falkien/Sunlu_S8_Switchwire_Conversion/Pics/Front Skirt.jpg

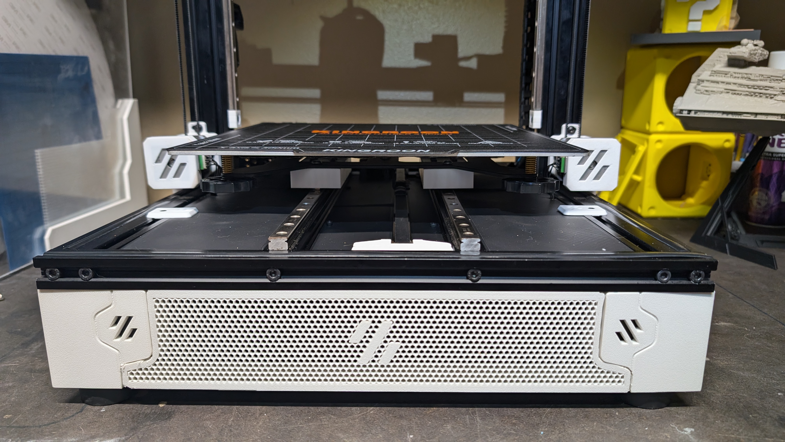
Pics/Front Skirt.jpg
