falkien/Sunlu_S8_Switchwire_Conversion/Pics/Overhead No Bed 4.jpg

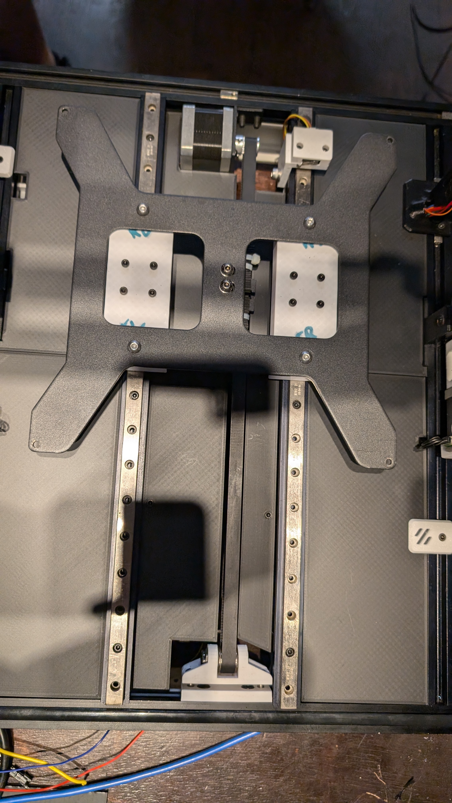
Pics/Overhead No Bed 4.jpg
