falkien/Sunlu_S8_Switchwire_Conversion/Pics/Overhead No Bed Rear 2.jpg

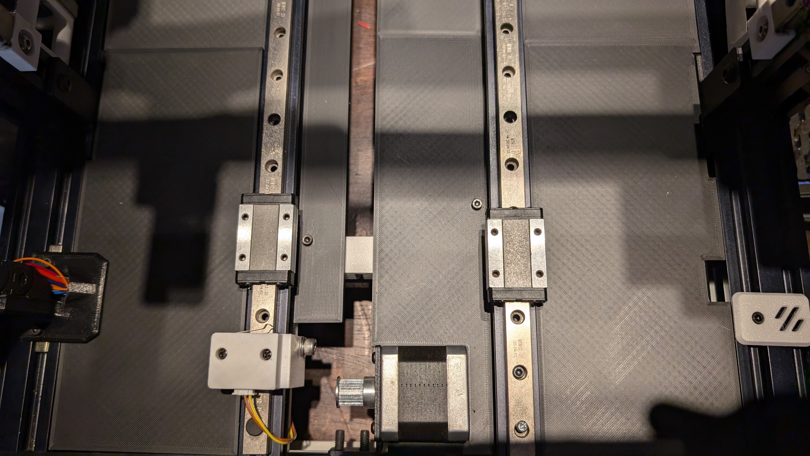
Pics/Overhead No Bed Rear 2.jpg
