falkien/Sunlu_S8_Switchwire_Conversion/Pics/Overhead No Bed Rear.jpg

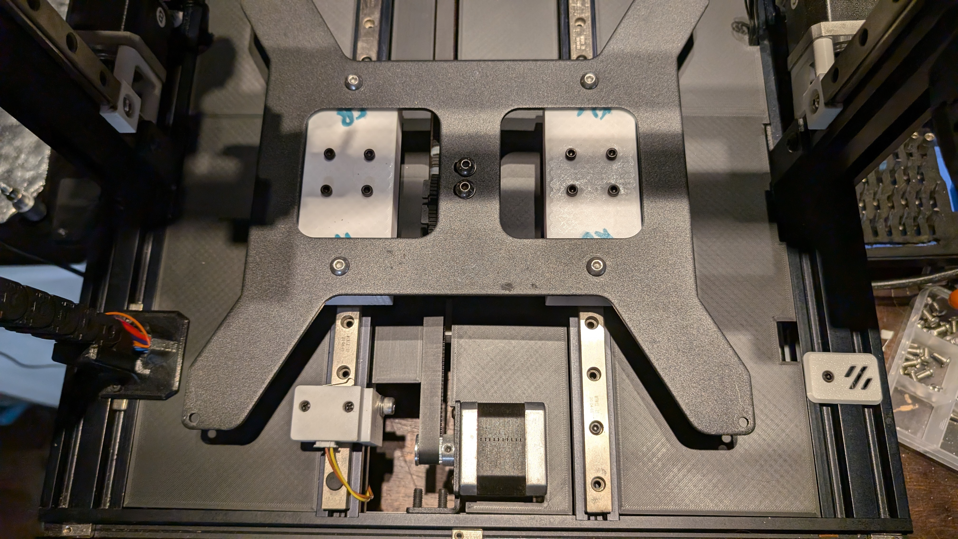
Pics/Overhead No Bed Rear.jpg
