falkien/Sunlu_S8_Switchwire_Conversion/Pics/Real All.jpg

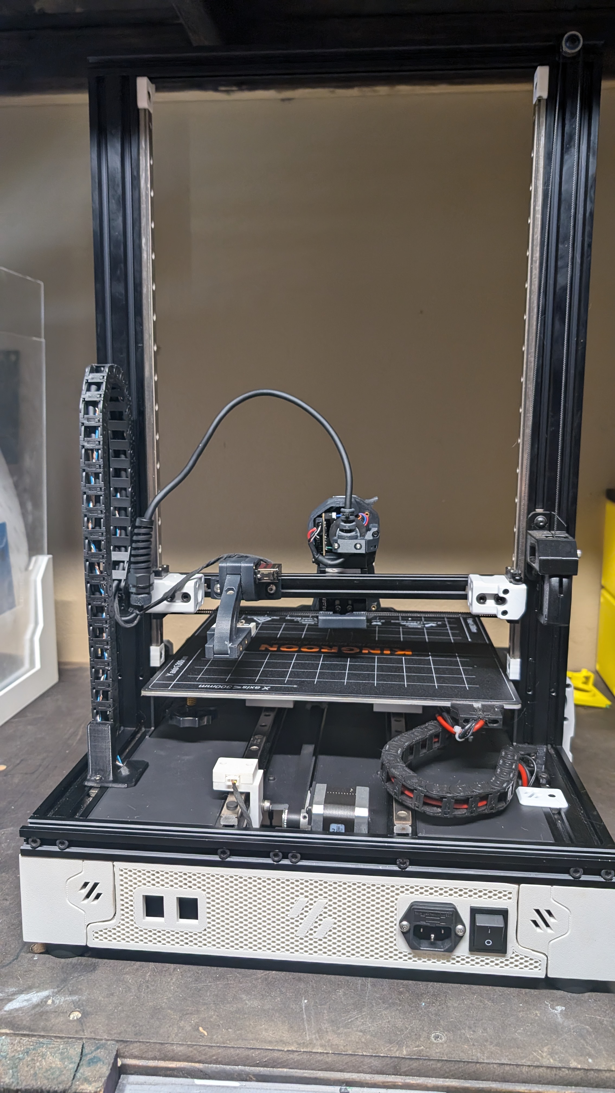
Pics/Real All.jpg
