falkien/Sunlu_S8_Switchwire_Conversion/Pics/Rear left.jpg

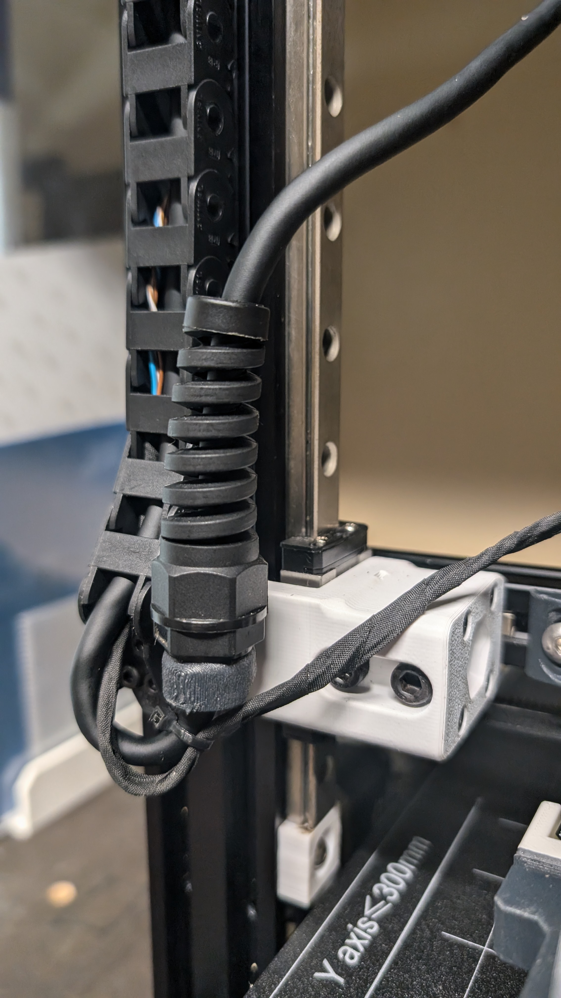
Pics/Rear left.jpg
