falkien/Sunlu_S8_Switchwire_Conversion/Pics/Rear Lower Chain.jpg

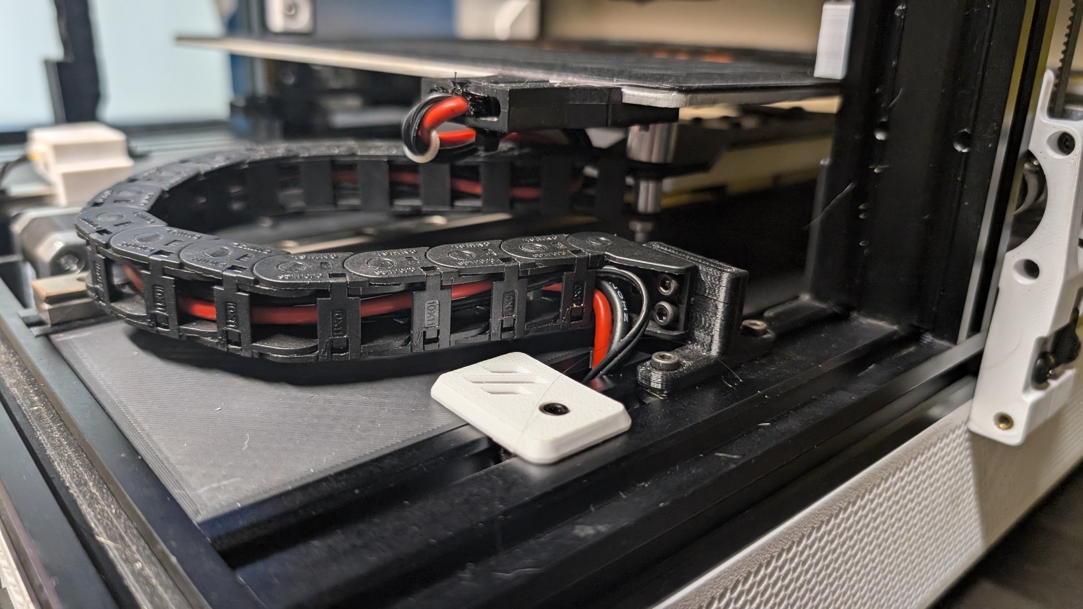
Pics/Rear Lower Chain.jpg
