falkien/Sunlu_S8_Switchwire_Conversion/Pics/Rear Skirt.jpg

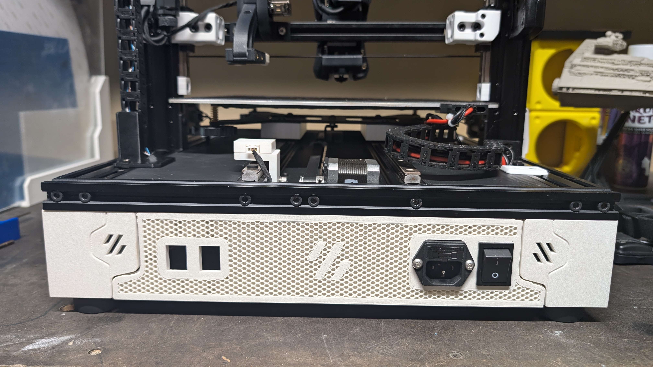
Pics/Rear Skirt.jpg
