falkien/Sunlu_S8_Switchwire_Conversion/Pics/Rear Toolhead Wide.jpg

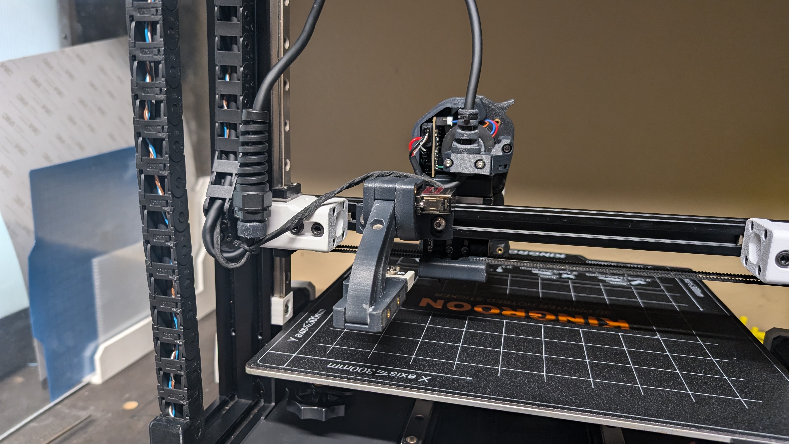
Pics/Rear Toolhead Wide.jpg
