falkien/Sunlu_S8_Switchwire_Conversion/Pics/Rear Toolhead.jpg

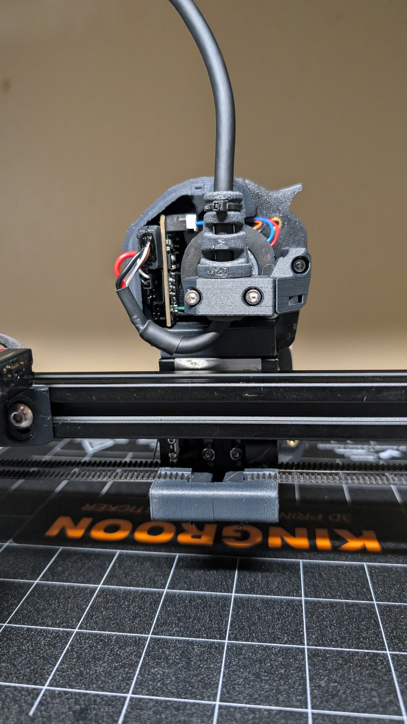
Pics/Rear Toolhead.jpg
