falkien/Sunlu_S8_Switchwire_Conversion/Pics/Rear Verticle Chain.jpg

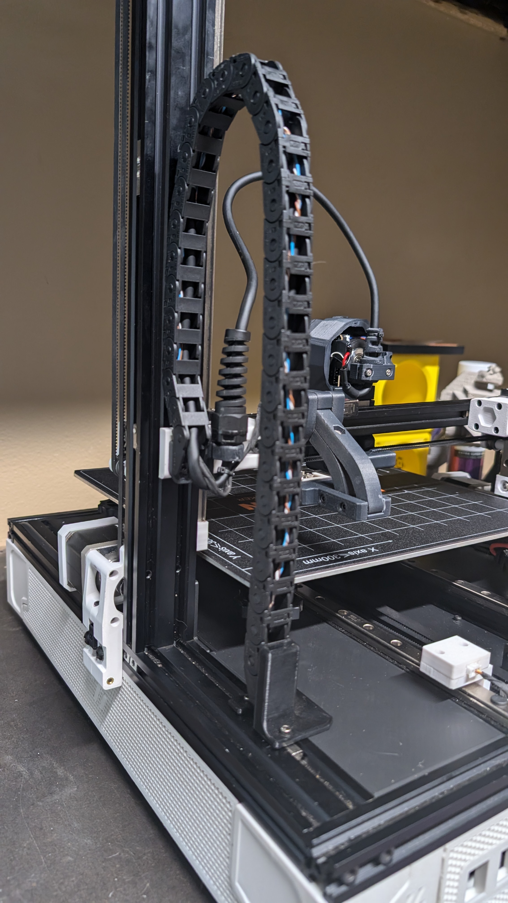
Pics/Rear Verticle Chain.jpg
