falkien/Sunlu_S8_Switchwire_Conversion/Pics/Right Main.jpg

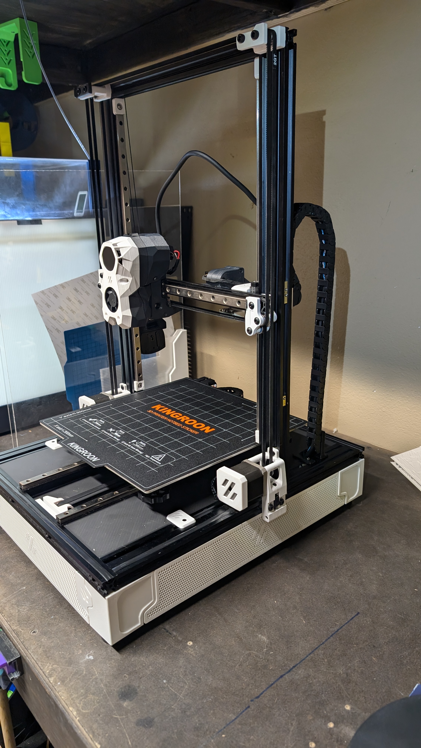
Pics/Right Main.jpg
