falkien/Sunlu_S8_Switchwire_Conversion/Pics/Right Skirt.jpg

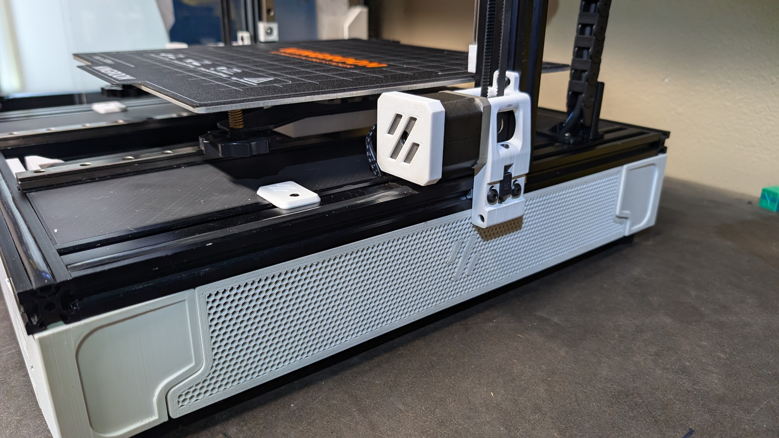
Pics/Right Skirt.jpg
