falkien/Sunlu_S8_Switchwire_Conversion/STL's/X axis/Swichwire_reverse_bowden_.stl

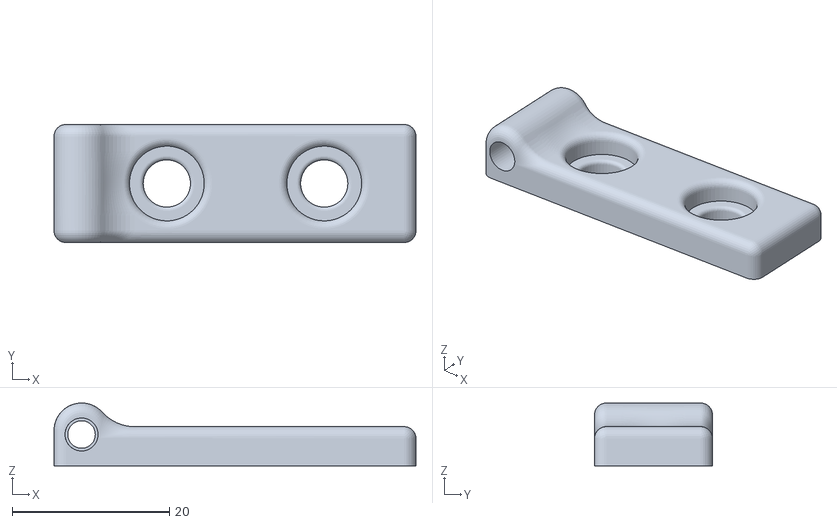
[picture p37: CAD file, 2024-08-12]
STL's/X axis/Swichwire_reverse_bowden_.stl
46.0 x 15.0 x 8.00
