falkien/Sunlu_S8_Switchwire_Conversion/STL's/Y axis/Sunlu_Y_Axis_rail_adaptor.stl

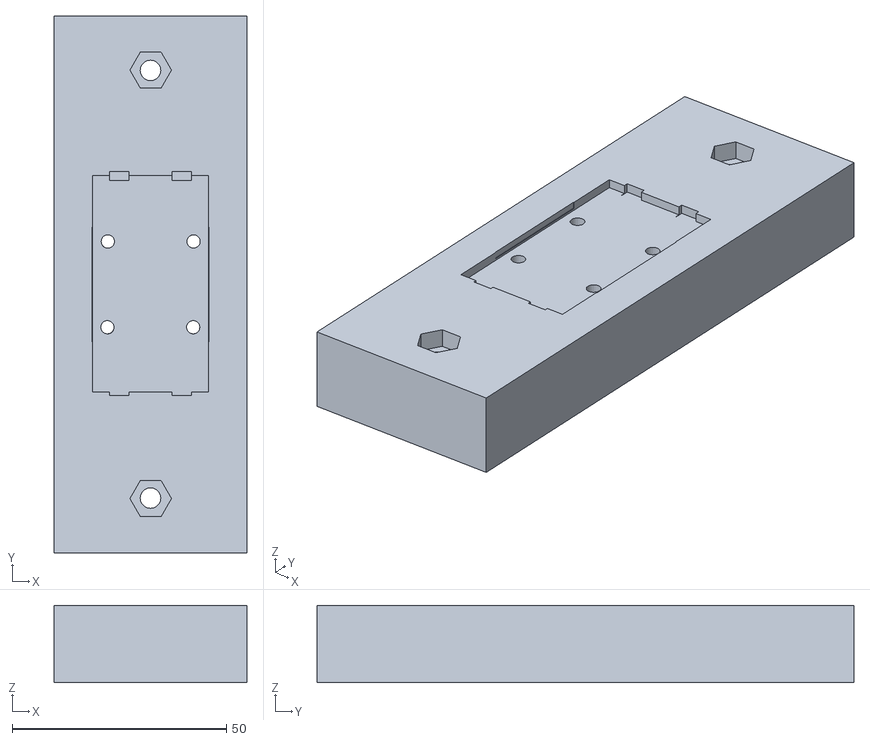
[picture p38: CAD file, 2024-01-11]
STL's/Y axis/Sunlu_Y_Axis_rail_adaptor.stl
45.0 x 125.2 x 18.0
