falkien/Sunlu_S8_Switchwire_Conversion/STL's/Z axis/keybak_mount_plate_b.stl

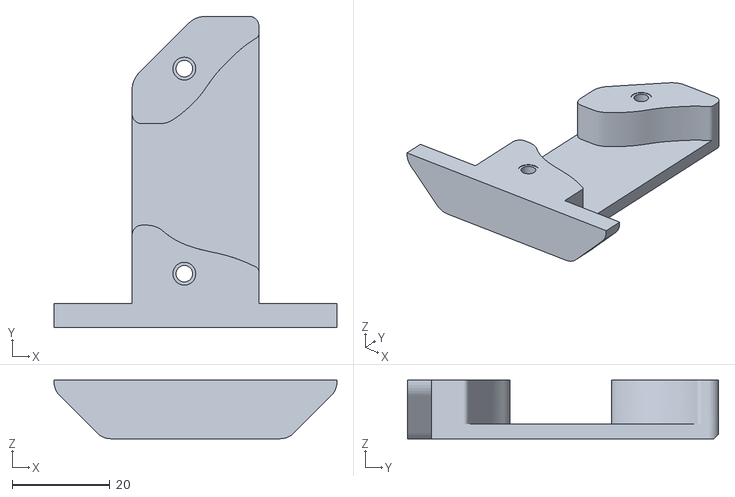
[picture p39: CAD file, 2024-01-11]
STL's/Z axis/keybak_mount_plate_b.stl
58.0 x 63.8 x 12.0
