falkien/Sunlu_S8_Switchwire_Conversion/STL's/Electronic Covers/Switchwire_Sunlu_S8_Left_Center.step

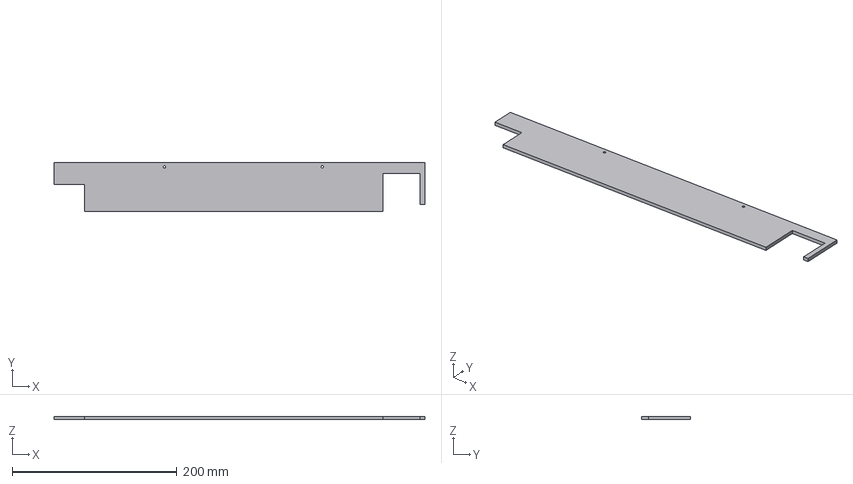
[picture p40: CAD file, 2024-08-11]
STL's/Electronic Covers/Switchwire_Sunlu_S8_Left_Center.step
450.0 x 60.0 x 4.00 mm
