falkien/Sunlu_S8_Switchwire_Conversion/STL's/Electronics_Bay/RPI fan mount bottom.stl

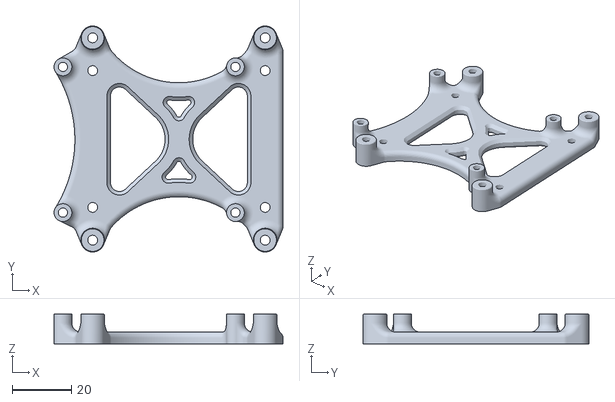
[picture p41: CAD file, 2024-08-12]
STL's/Electronics_Bay/RPI fan mount bottom.stl
77.0 x 76.0 x 10.0
