falkien/Sunlu_S8_Switchwire_Conversion/STL's/Skirt_New/Sunlu-S8_Switchwire-front-noscreen_274.1mm.3mf

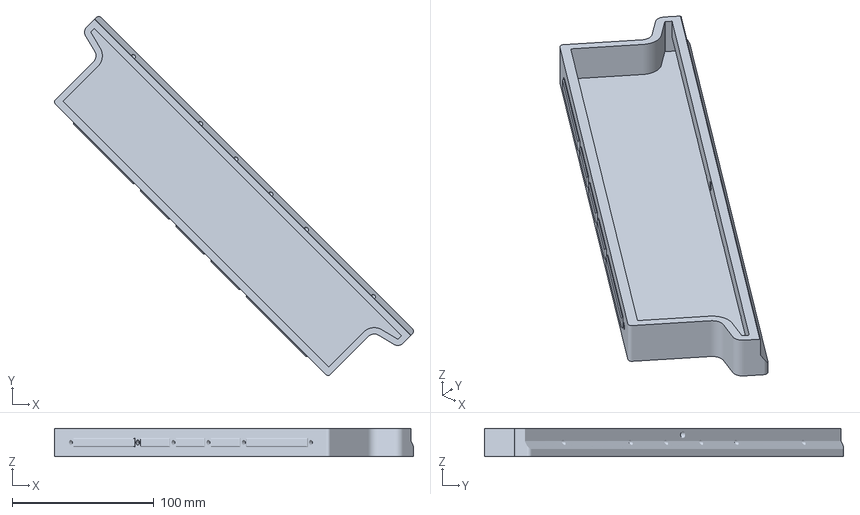
[picture p42: CAD file, 2024-07-28]
STL's/Skirt_New/Sunlu-S8_Switchwire-front-noscreen_274.1mm.3mf
253.2 x 253.2 x 20.0 mm
