falkien/Sunlu_S8_Switchwire_Conversion/STL's/Stealthburner/[o]_stealthburner_LED_diffuser_mask.stl

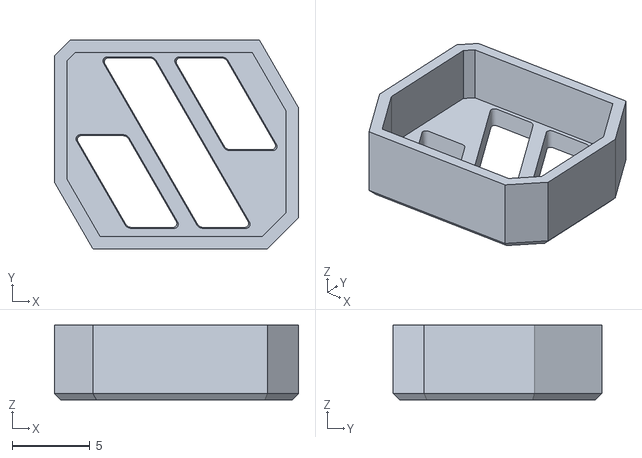
[picture p43: CAD file, 2024-01-11]
STL's/Stealthburner/[o]_stealthburner_LED_diffuser_mask.stl
15.7 x 13.4 x 4.80
