falkien/Sunlu_S8_Switchwire_Conversion/STL's/Stealthburner/ADXL345_Mounts/sb_adxl_mount_adafruit_19mm_c_c.stl

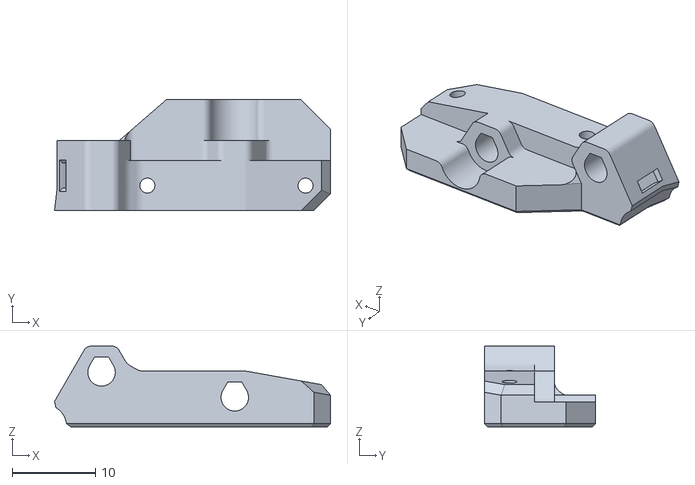
[picture p44: CAD file, 2024-01-11]
STL's/Stealthburner/ADXL345_Mounts/sb_adxl_mount_adafruit_19mm_c_c.stl
33.2 x 13.4 x 9.70
