falkien/Sunlu_S8_Switchwire_Conversion/STL's/Toolhead_Cable_Management/cw2-pug-mount-arm.3mf

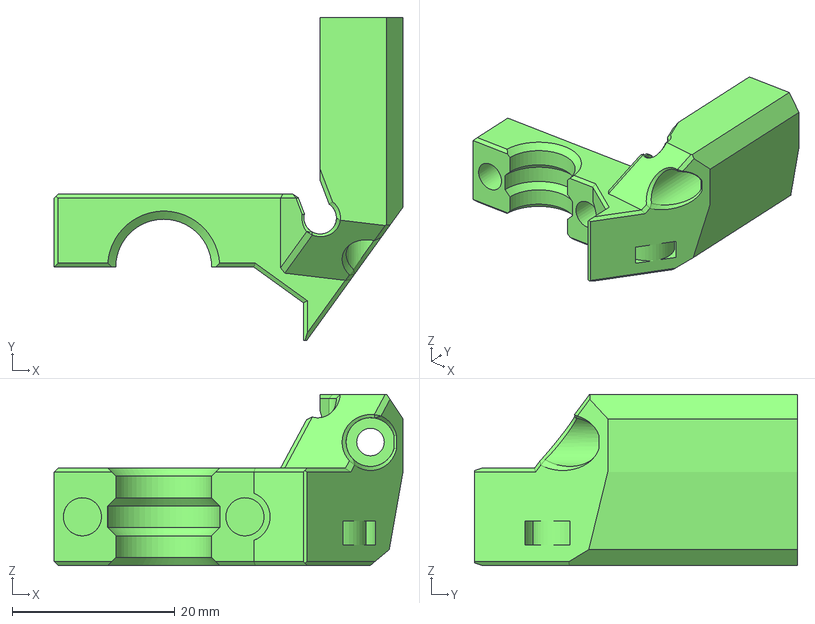
[picture p45: CAD file, 2024-08-12]
STL's/Toolhead_Cable_Management/cw2-pug-mount-arm.3mf
42.9 x 39.7 x 21.1 mm
