falkien/Sunlu_S8_Switchwire_Conversion/STL's/X axis/Knomi Screen/StealthBurner Mounting Plate for KNOMI.STL

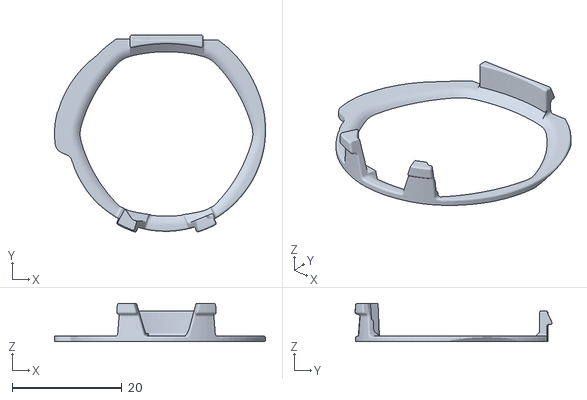
[picture p46: CAD file, 2024-01-11]
STL's/X axis/Knomi Screen/StealthBurner Mounting Plate for KNOMI.STL
38.4 x 35.8 x 7.00
