falkien/Sunlu_S8_Switchwire_Conversion/STL's/X axis/xz_block_right_b.stl

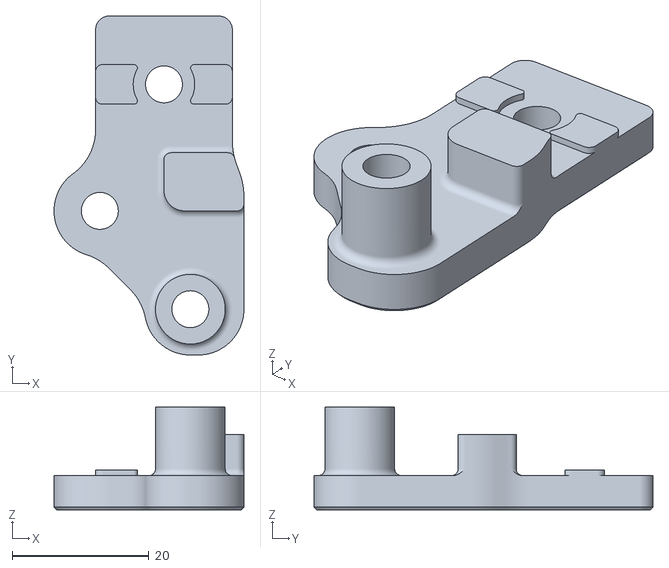
[picture p47: CAD file, 2024-01-11]
STL's/X axis/xz_block_right_b.stl
27.8 x 49.6 x 15.0
