falkien/Sunlu_S8_Switchwire_Conversion/STL's/Y axis/Sunlu_Y-Axis_Brkt_V1.stl

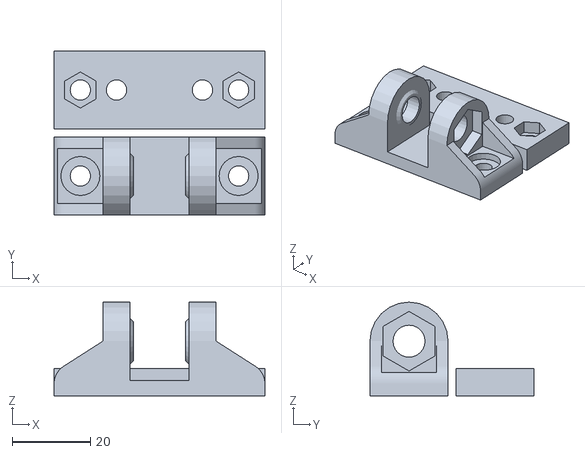
[picture p48: CAD file, 2024-01-11]
STL's/Y axis/Sunlu_Y-Axis_Brkt_V1.stl
54.0 x 42.0 x 24.0
