falkien/Sunlu_S8_Switchwire_Conversion/STL's/Z axis/Nema17 Motor Cover - Voron Logo for SW_inserted_90.stl

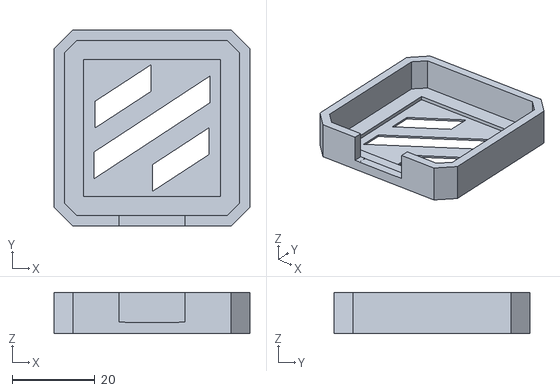
[picture p49: CAD file, 2024-01-11]
STL's/Z axis/Nema17 Motor Cover - Voron Logo for SW_inserted_90.stl
47.3 x 47.3 x 10.00
