falkien/Sunlu_S8_Switchwire_Conversion/STL's/Electronic Covers/Switchwire_Sunlu_S8_Right_Center.step

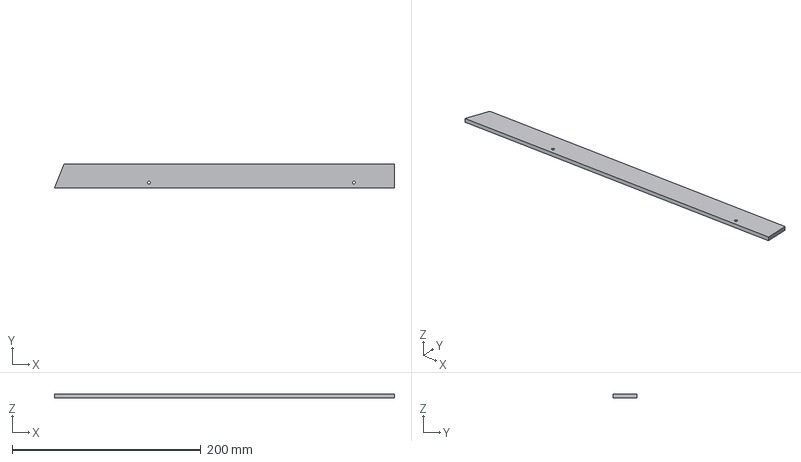
[picture p50: CAD file, 2024-08-11]
STL's/Electronic Covers/Switchwire_Sunlu_S8_Right_Center.step
360.0 x 25.0 x 4.00 mm
