falkien/Sunlu_S8_Switchwire_Conversion/STL's/Electronics_Bay/CableDuctCover_small.stl

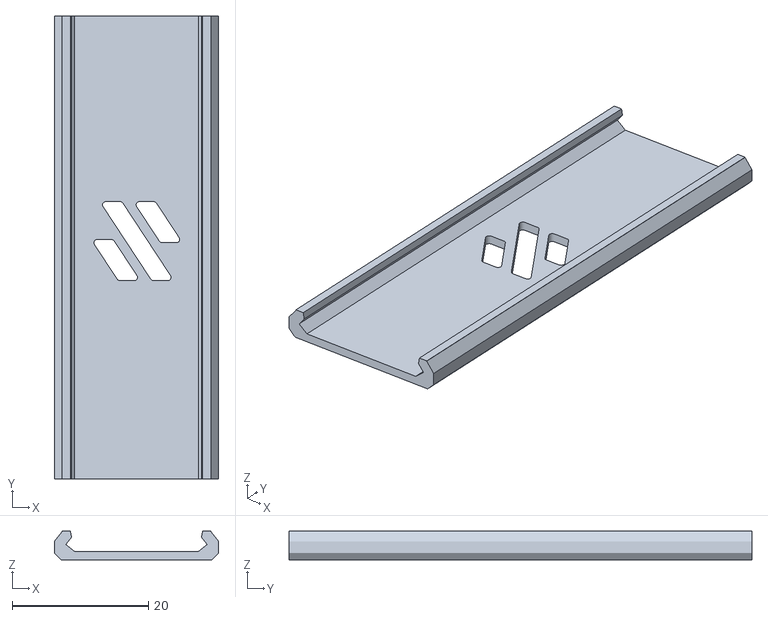
[picture p51: CAD file, 2024-08-12]
STL's/Electronics_Bay/CableDuctCover_small.stl
24.1 x 68.0 x 4.20
