falkien/Sunlu_S8_Switchwire_Conversion/STL's/Skirt_New/Sunlu-S8_Switchwire-Front-BTT-TFT50-V2_1x.3mf

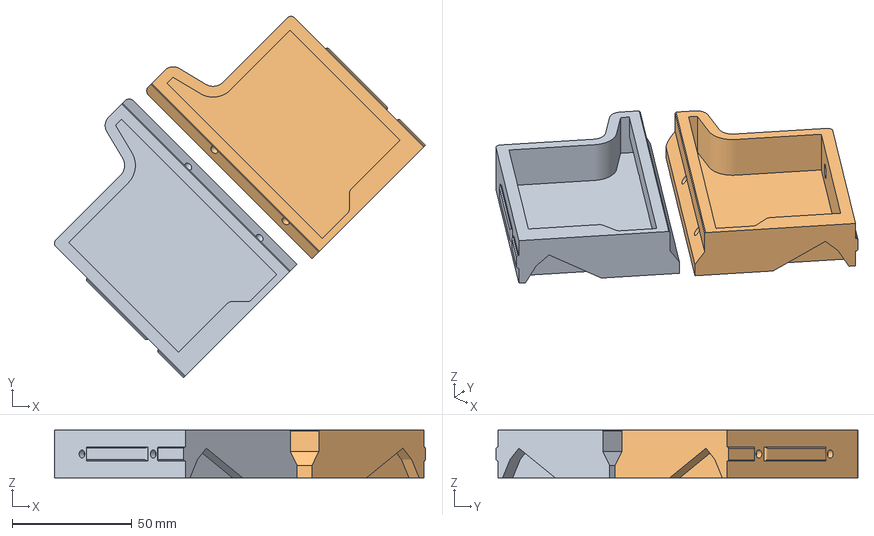
[picture p52: CAD file, 2024-07-27]
STL's/Skirt_New/Sunlu-S8_Switchwire-Front-BTT-TFT50-V2_1x.3mf
154.9 x 150.9 x 20.0 mm
Front-TFT50-A-250
Front-TFT50-B-250
