falkien/Sunlu_S8_Switchwire_Conversion/STL's/Stealthburner/[c]_stealthburner_LED_diffuser.stl

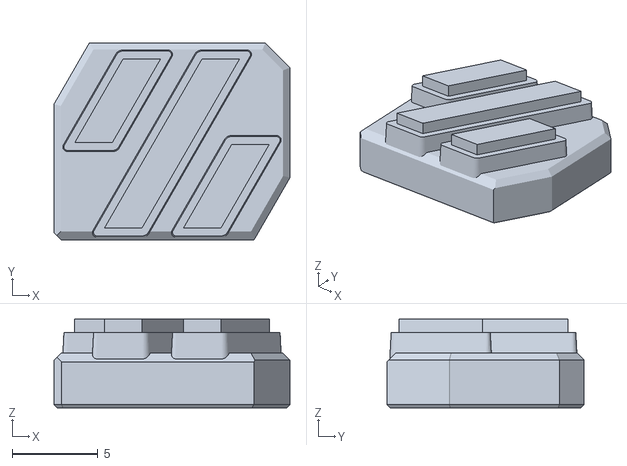
[picture p53: CAD file, 2024-01-11]
STL's/Stealthburner/[c]_stealthburner_LED_diffuser.stl
13.8 x 11.5 x 5.20
