falkien/Sunlu_S8_Switchwire_Conversion/STL's/Toolhead_Cable_Management/pug_v4_s_70mm.stl

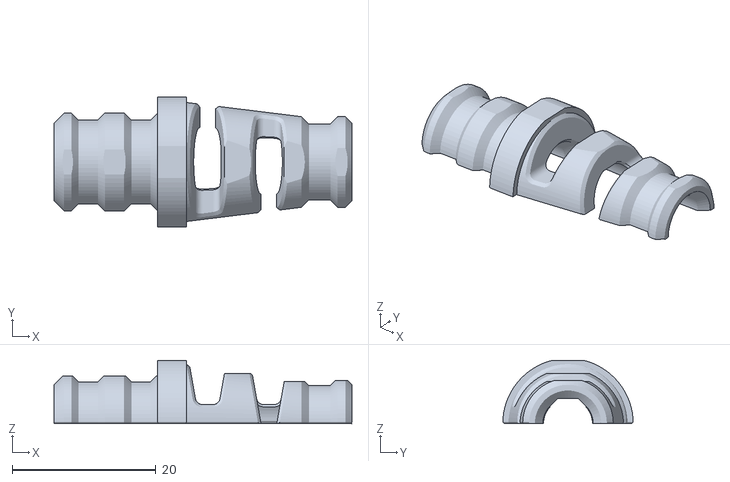
[picture p54: CAD file, 2024-08-12]
STL's/Toolhead_Cable_Management/pug_v4_s_70mm.stl
41.4 x 18.1 x 8.80
