falkien/Sunlu_S8_Switchwire_Conversion/STL's/X axis/xz_block_right_a.stl

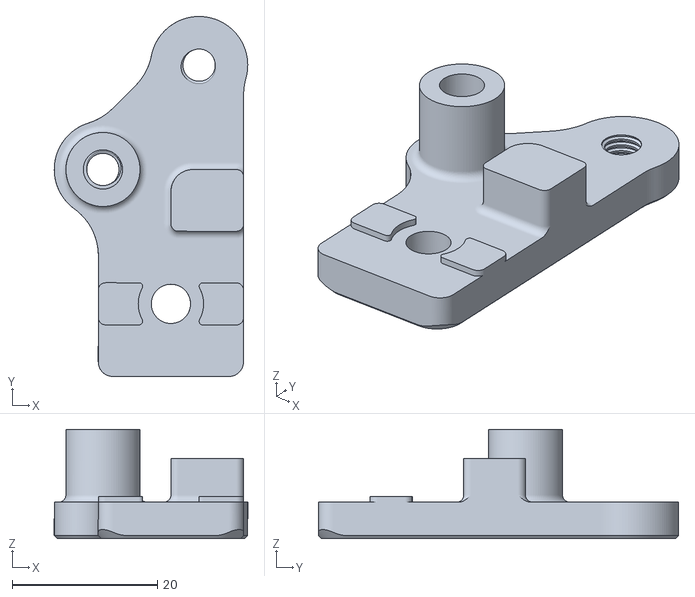
[picture p55: CAD file, 2024-01-11]
STL's/X axis/xz_block_right_a.stl
26.7 x 49.6 x 15.0
