falkien/Sunlu_S8_Switchwire_Conversion/STL's/Y axis/Sunlu_Y_Axis_endstop.stl

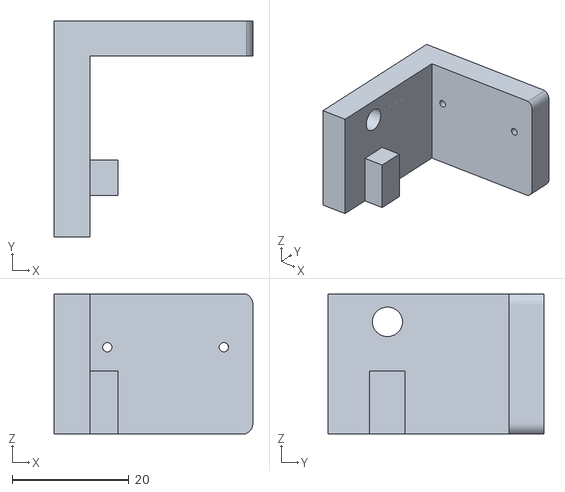
[picture p56: CAD file, 2024-01-11]
STL's/Y axis/Sunlu_Y_Axis_endstop.stl
34.1 x 37.0 x 24.0
