falkien/Sunlu_S8_Switchwire_Conversion/STL's/Z axis/z_motor_mount_a.stl

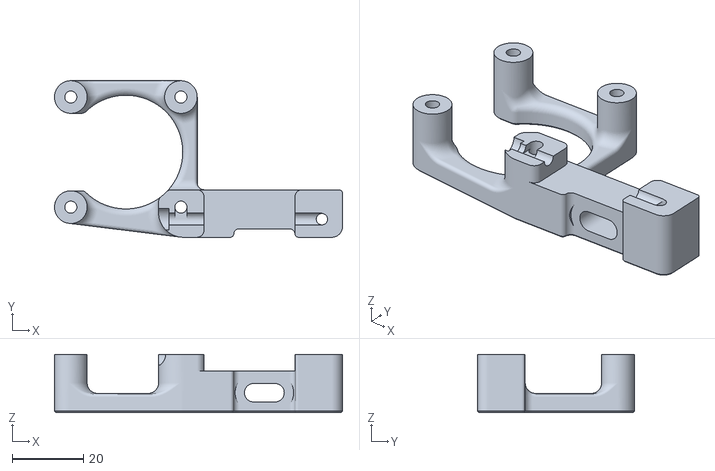
[picture p57: CAD file, 2024-01-11]
STL's/Z axis/z_motor_mount_a.stl
81.1 x 44.1 x 16.4
