falkien/Sunlu_S8_Switchwire_Conversion/STL's/Electronic Covers/Switchwire_Sunlu_S8_Right_Front.step

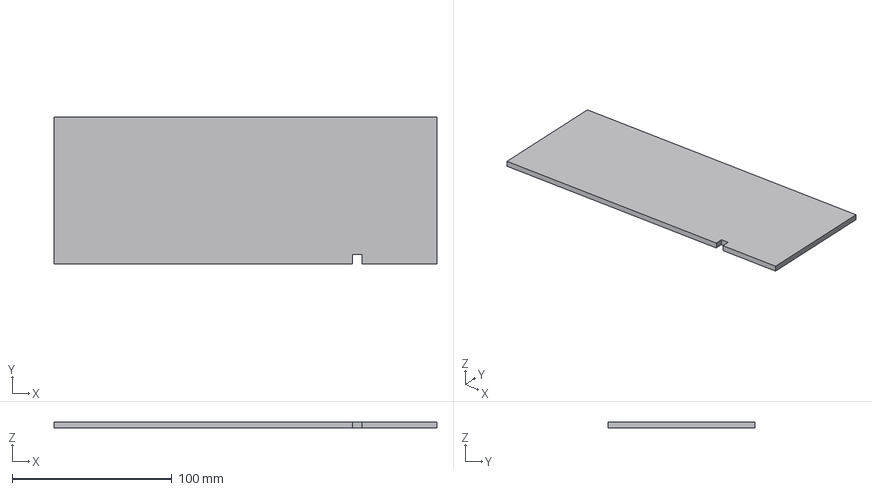
[picture p58: CAD file, 2024-08-11]
STL's/Electronic Covers/Switchwire_Sunlu_S8_Right_Front.step
240.0 x 92.0 x 4.00 mm
