falkien/Sunlu_S8_Switchwire_Conversion/STL's/Electronics_Bay/CableDuctCover_large.stl

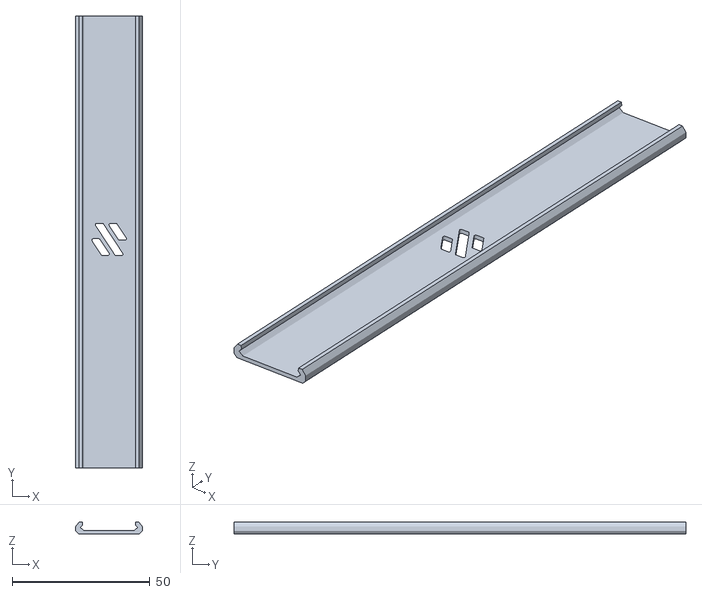
[picture p59: CAD file, 2024-08-12]
STL's/Electronics_Bay/CableDuctCover_large.stl
24.1 x 164.0 x 4.20
