falkien/Sunlu_S8_Switchwire_Conversion/STL's/Skirt_New/Trident-original-Side-skirt-V2-350_2x.3mf

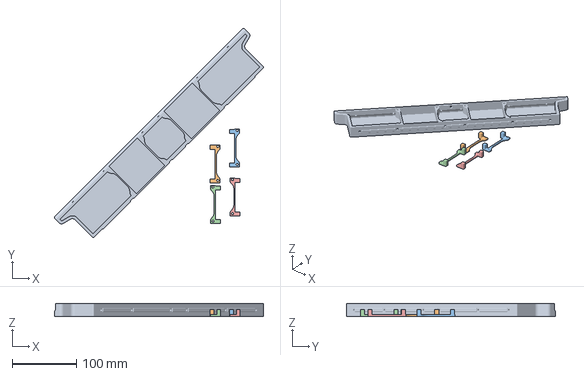
[picture p60: CAD file, 2024-07-27]
STL's/Skirt_New/Trident-original-Side-skirt-V2-350_2x.3mf
324.4 x 324.4 x 20.0 mm
F1-Side-skirt-mid-V1.stl
Side-skirt-fanholder_V2.stl x 4
