falkien/Sunlu_S8_Switchwire_Conversion/STL's/Toolhead_Cable_Management/Support pg7 - 1.stl

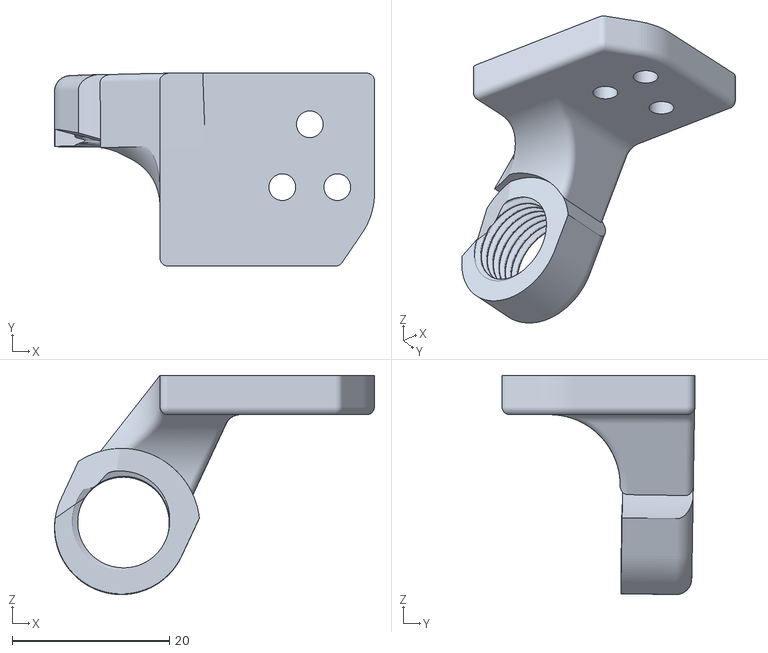
[picture p61: CAD file, 2024-08-12]
STL's/Toolhead_Cable_Management/Support pg7 - 1.stl
40.7 x 24.6 x 27.9
