falkien/Sunlu_S8_Switchwire_Conversion/STL's/Y axis/Sunlu_Y_chain_frame_anchor_igus.stl

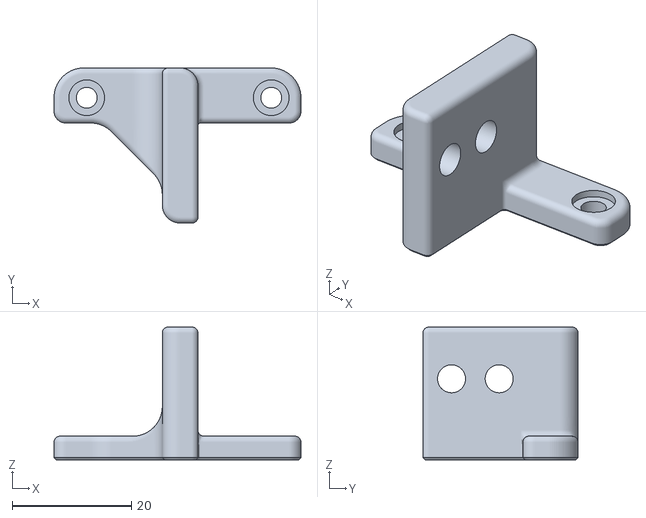
[picture p62: CAD file, 2024-01-11]
STL's/Y axis/Sunlu_Y_chain_frame_anchor_igus.stl
41.5 x 26.1 x 22.3
