falkien/Sunlu_S8_Switchwire_Conversion/STL's/Z axis/z_carriage_stop_V2_x4.stl

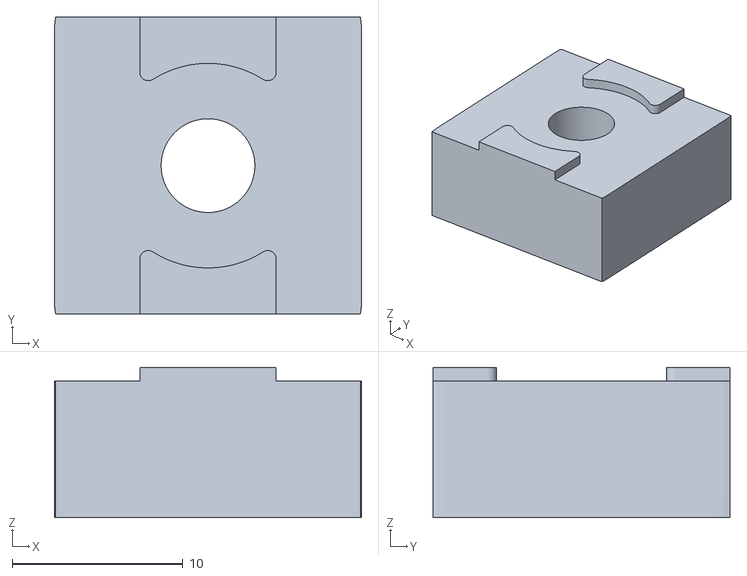
[picture p63: CAD file, 2024-01-11]
STL's/Z axis/z_carriage_stop_V2_x4.stl
18.0 x 17.4 x 8.80
