falkien/Sunlu_S8_Switchwire_Conversion/STL's/Electronic Covers/Switchwire_Sunlu_S8_Left_Rear.step

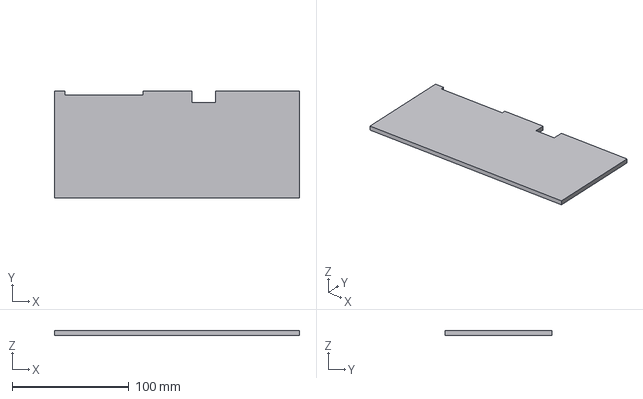
[picture p64: CAD file, 2024-08-11]
STL's/Electronic Covers/Switchwire_Sunlu_S8_Left_Rear.step
210.0 x 92.0 x 4.00 mm
