falkien/Sunlu_S8_Switchwire_Conversion/STL's/Electronics_Bay/CableDuctBody_medium.stl

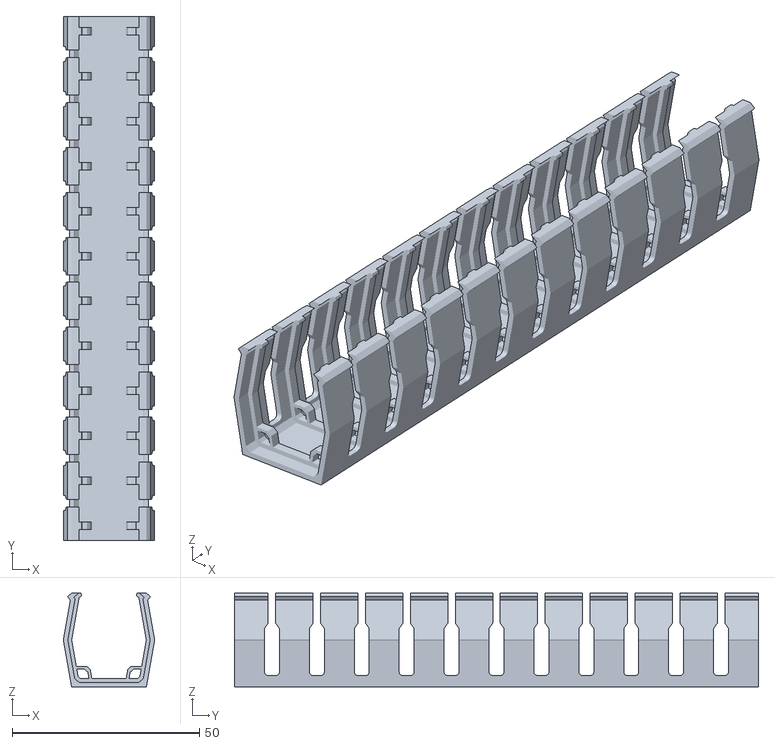
[picture p65: CAD file, 2024-08-12]
STL's/Electronics_Bay/CableDuctBody_medium.stl
24.4 x 140.0 x 25.0
