falkien/Sunlu_S8_Switchwire_Conversion/STL's/Skirt_New/Sunlu-S8_Switchwire-Optional_FootV2-B_2x.stl

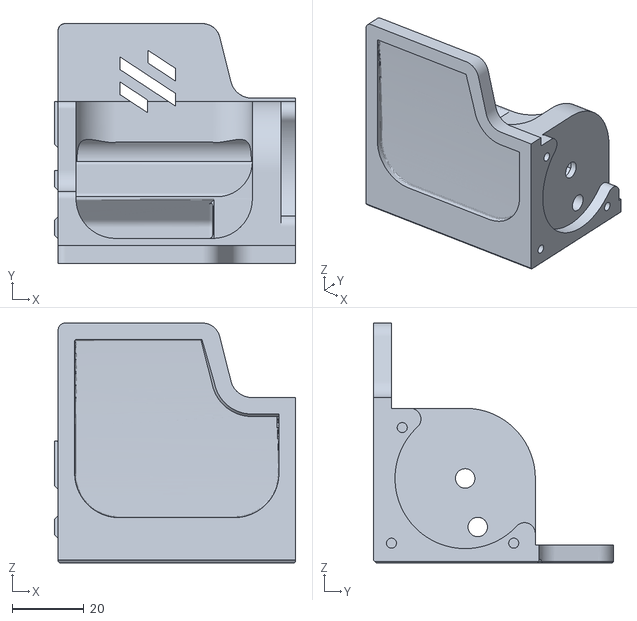
[picture p66: CAD file, 2024-07-27]
STL's/Skirt_New/Sunlu-S8_Switchwire-Optional_FootV2-B_2x.stl
67.0 x 66.7 x 66.7
