falkien/Sunlu_S8_Switchwire_Conversion/STL's/Toolhead_Cable_Management/Support pg7 - 2.stl

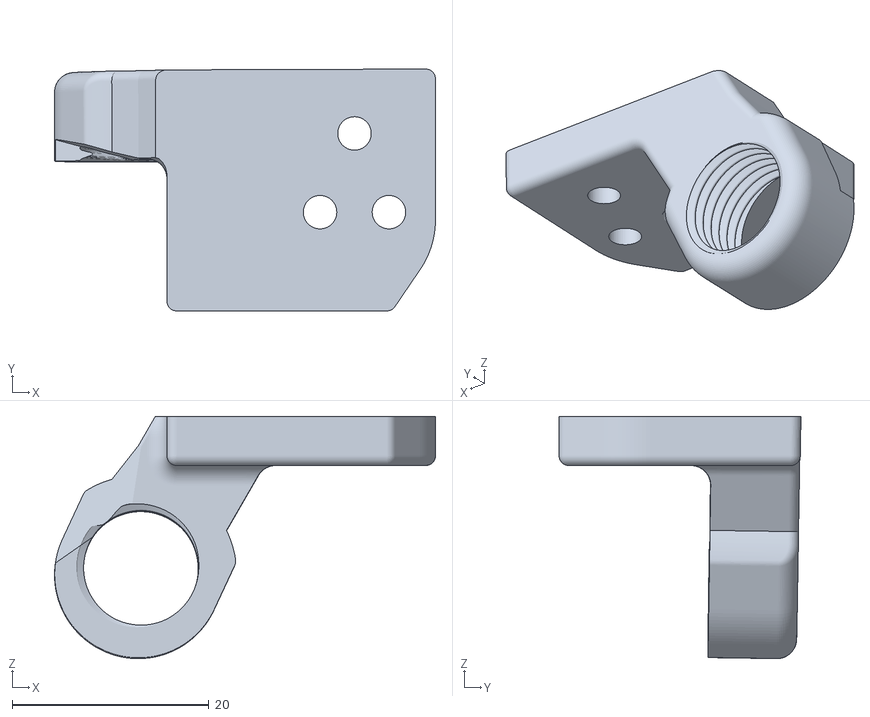
[picture p67: CAD file, 2024-08-12]
STL's/Toolhead_Cable_Management/Support pg7 - 2.stl
38.7 x 24.6 x 24.6
