falkien/Sunlu_S8_Switchwire_Conversion/STL's/X axis/xz_block_left_a.stl

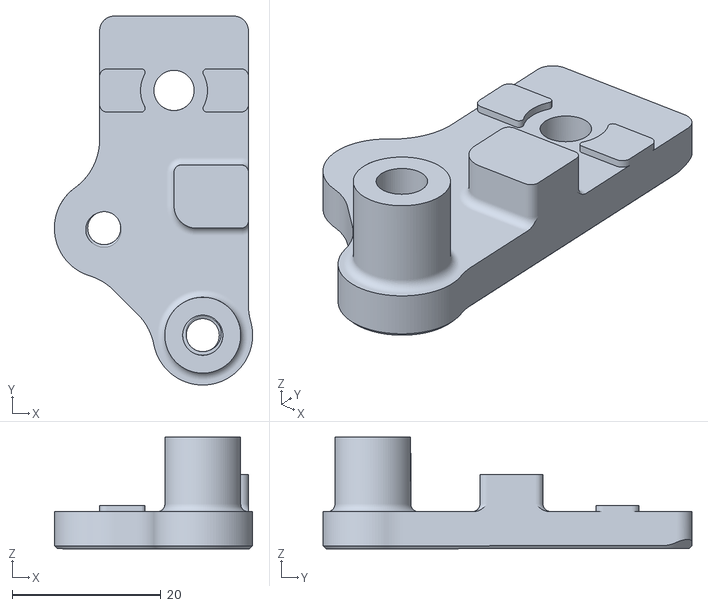
[picture p68: CAD file, 2024-01-11]
STL's/X axis/xz_block_left_a.stl
26.6 x 49.6 x 15.0
