falkien/Sunlu_S8_Switchwire_Conversion/STL's/Y axis/Sunlu_Y_Axis_endstop_cover.STL

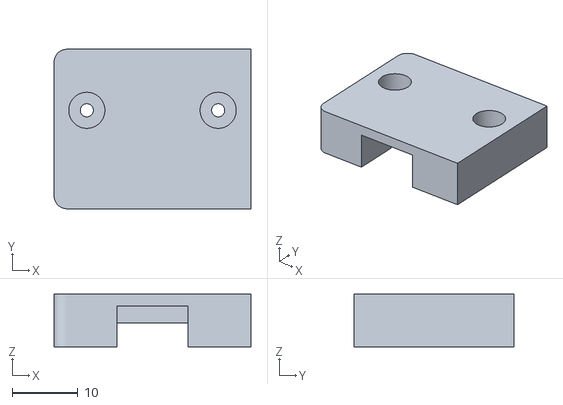
[picture p69: CAD file, 2024-01-11]
STL's/Y axis/Sunlu_Y_Axis_endstop_cover.STL
30.0 x 24.3 x 8.00
