falkien/Sunlu_S8_Switchwire_Conversion/STL's/Z axis/keybak_mount_plate_a.stl

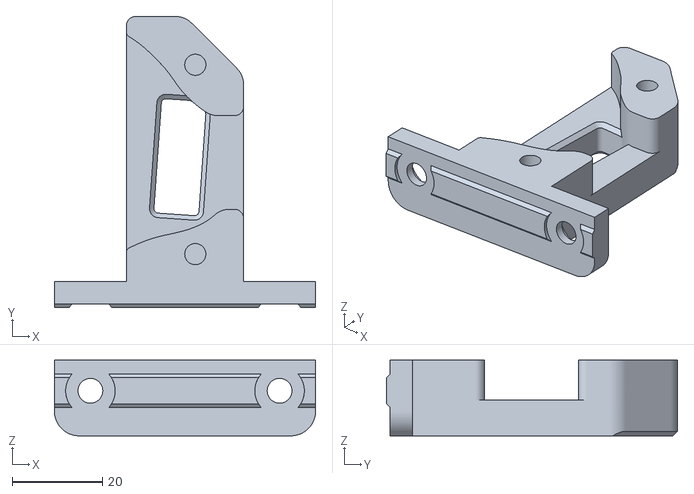
[picture p70: CAD file, 2024-01-11]
STL's/Z axis/keybak_mount_plate_a.stl
58.0 x 64.6 x 16.8
