falkien/Sunlu_S8_Switchwire_Conversion/STL's/Electronic Covers/Switchwire Sunlu S8 Panels.step

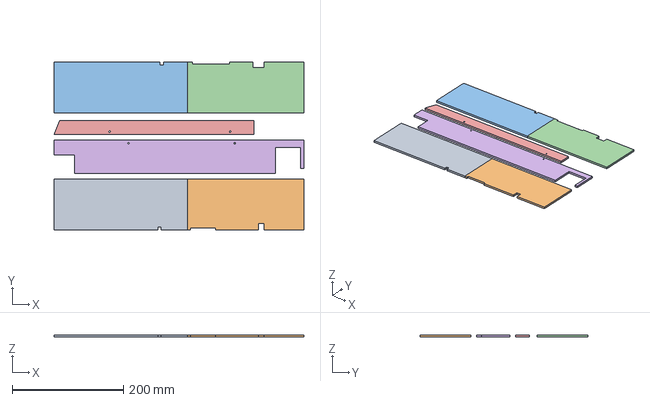
[picture p71: CAD file, 2024-08-11]
STL's/Electronic Covers/Switchwire Sunlu S8 Panels.step
450.0 x 303.0 x 4.00 mm
