falkien/Sunlu_S8_Switchwire_Conversion/STL's/Electronics_Bay/CableDuctBody_large.stl

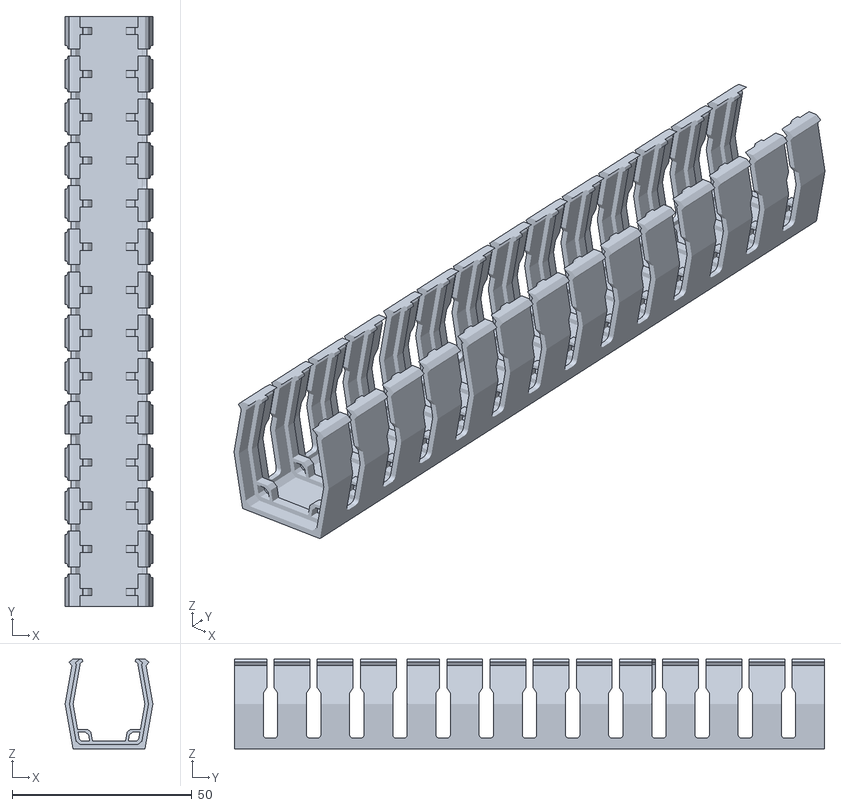
[picture p72: CAD file, 2024-08-12]
STL's/Electronics_Bay/CableDuctBody_large.stl
24.4 x 164.0 x 25.0
