falkien/Sunlu_S8_Switchwire_Conversion/STL's/Skirt_New/Sunlu-S8_Switchwire_Side_Skirt_354.74mm.3mf

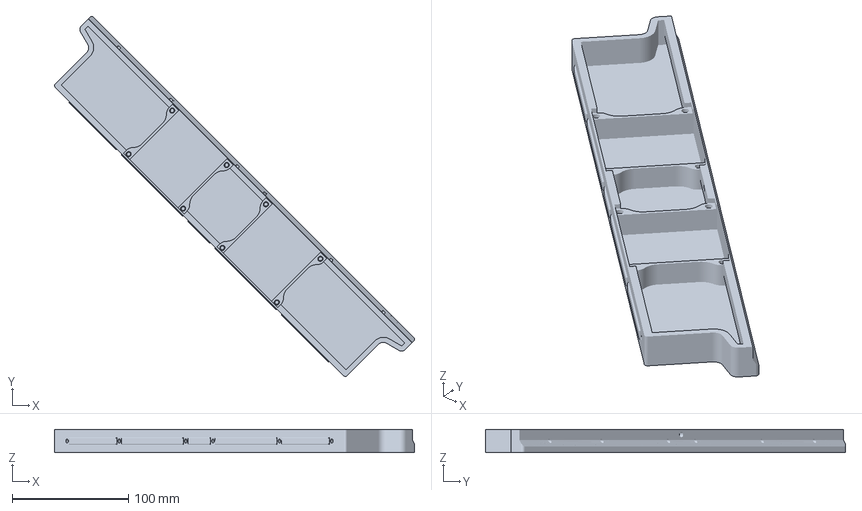
[picture p73: CAD file, 2024-07-27]
STL's/Skirt_New/Sunlu-S8_Switchwire_Side_Skirt_354.74mm.3mf
309.5 x 309.5 x 20.0 mm
