falkien/Sunlu_S8_Switchwire_Conversion/STL's/Stealthburner/ADXL345_Mounts/sb_adxl_mount_sparkfun_LIS3DH.stl

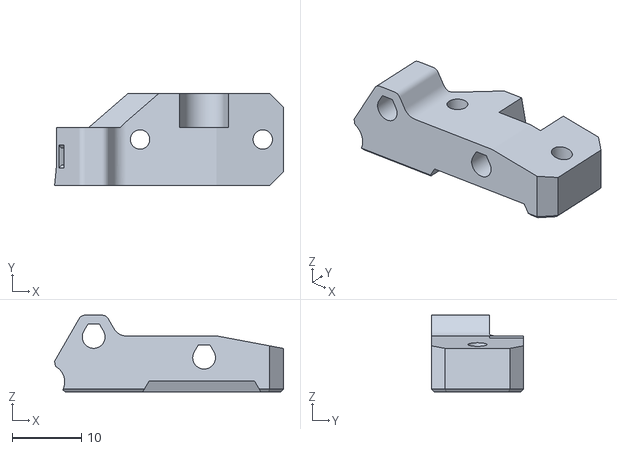
[picture p74: CAD file, 2024-01-11]
STL's/Stealthburner/ADXL345_Mounts/sb_adxl_mount_sparkfun_LIS3DH.stl
33.2 x 13.4 x 11.1
