falkien/Sunlu_S8_Switchwire_Conversion/STL's/X axis/upper_idler_support_a_left_original.stl

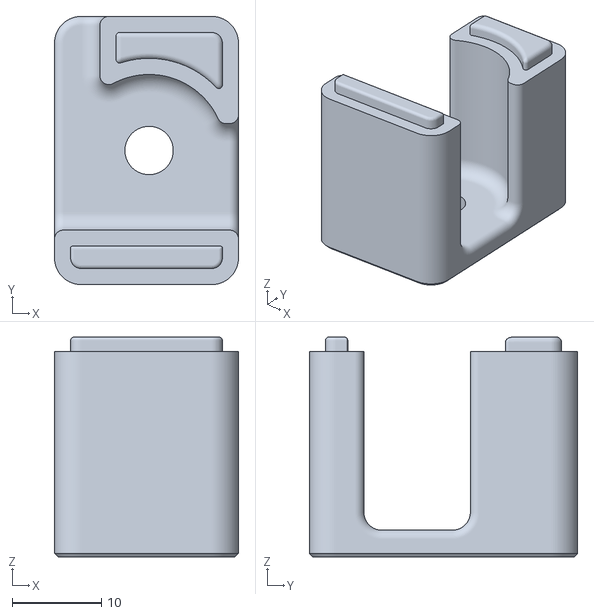
[picture p75: CAD file, 2024-01-11]
STL's/X axis/upper_idler_support_a_left_original.stl
20.6 x 30.0 x 24.6
