falkien/Sunlu_S8_Switchwire_Conversion/STL's/Electronics_Bay/CableDuctCover_medium.stl

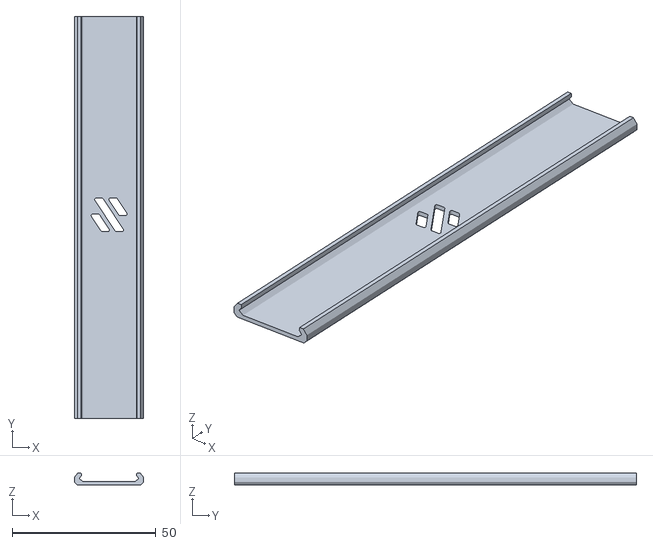
[picture p76: CAD file, 2024-08-12]
STL's/Electronics_Bay/CableDuctCover_medium.stl
24.1 x 140.0 x 4.20
