falkien/Sunlu_S8_Switchwire_Conversion/STL's/Z axis/keybak_idler_bracket.stl

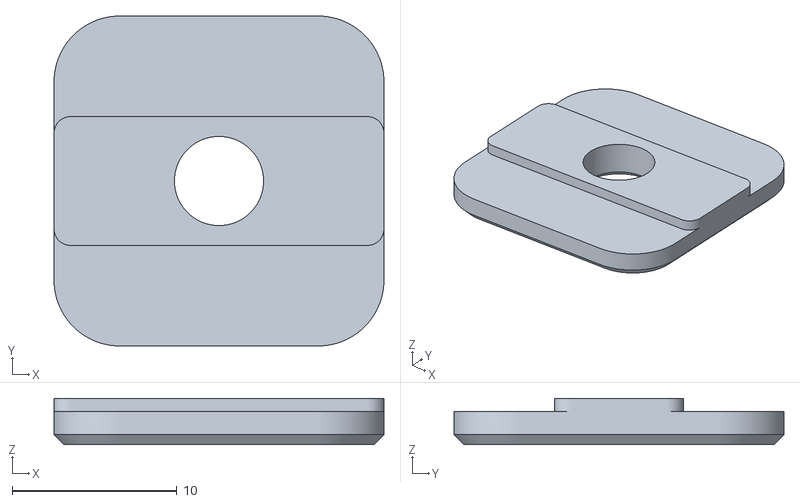
[picture p77: CAD file, 2024-01-11]
STL's/Z axis/keybak_idler_bracket.stl
20.0 x 20.0 x 2.80
