falkien/Sunlu_S8_Switchwire_Conversion/STL's/Electronics_Bay/CableDuctBody_small.stl

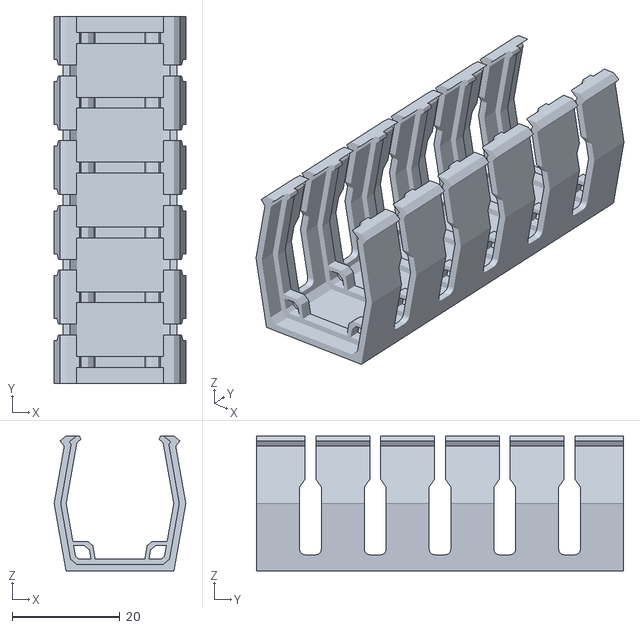
[picture p78: CAD file, 2024-08-12]
STL's/Electronics_Bay/CableDuctBody_small.stl
24.4 x 68.0 x 25.0
