falkien/Sunlu_S8_Switchwire_Conversion/STL's/X axis/[a]_upper_idler_support_b_right_alt.stl

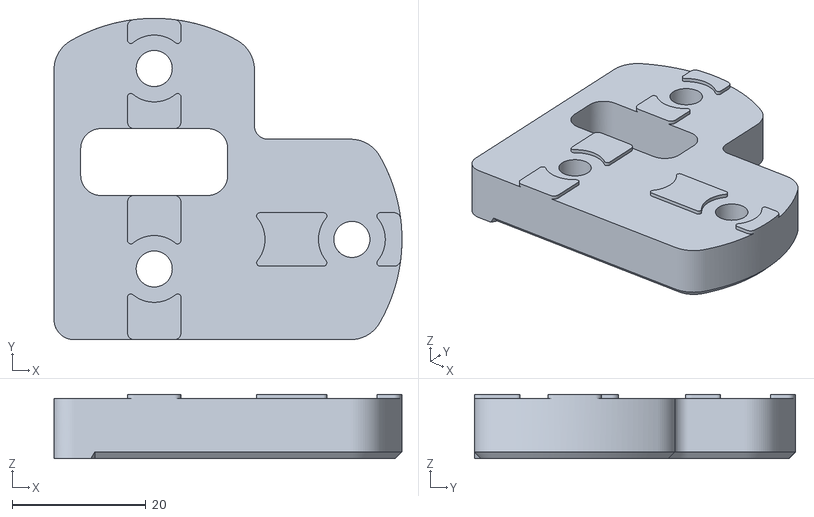
[picture p79: CAD file, 2024-01-11]
STL's/X axis/[a]_upper_idler_support_b_right_alt.stl
52.1 x 48.1 x 9.60
