falkien/Sunlu_S8_Switchwire_Conversion/STL's/Z axis/z_motor_mount_b.stl

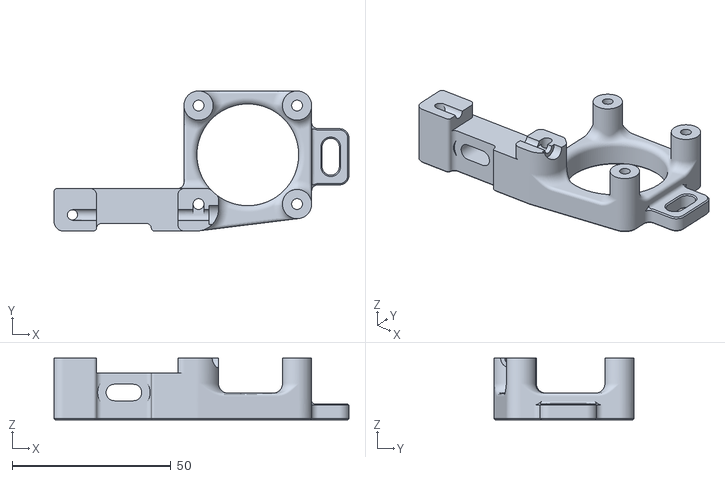
[picture p80: CAD file, 2024-01-11]
STL's/Z axis/z_motor_mount_b.stl
92.8 x 44.1 x 19.4
