falkien/Sunlu_S8_Switchwire_Conversion/STL's/Electronics_Bay/4010 fan mount for SKR mini e3 v3.stl

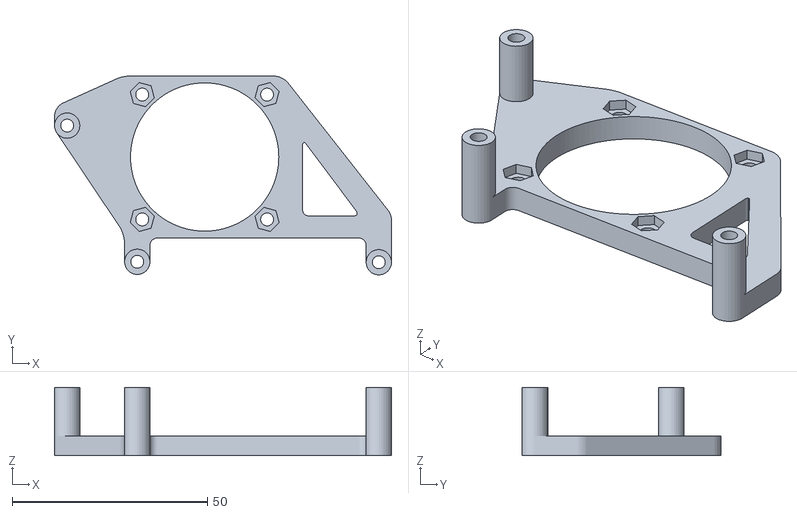
[picture p81: CAD file, 2024-08-12]
STL's/Electronics_Bay/4010 fan mount for SKR mini e3 v3.stl
86.4 x 51.0 x 17.5
