falkien/Sunlu_S8_Switchwire_Conversion/STL's/Skirt_New/Trident-original-Side-skirt-V2-350_2x_RESIZE.3mf

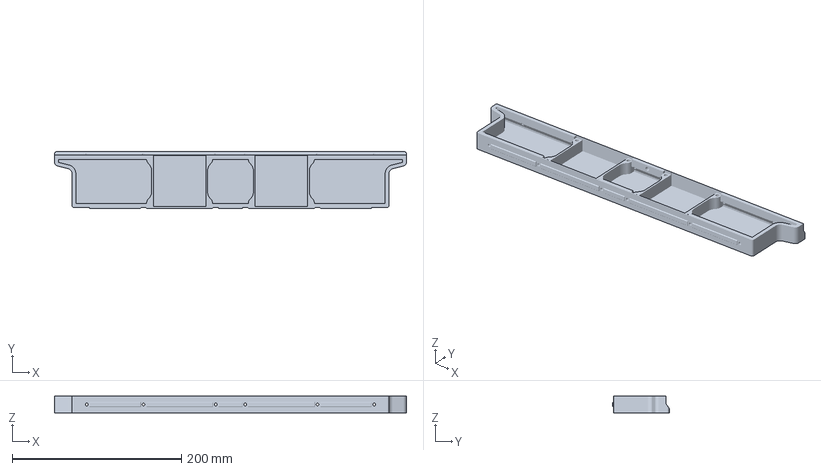
[picture p82: CAD file, 2024-07-27]
STL's/Skirt_New/Trident-original-Side-skirt-V2-350_2x_RESIZE.3mf
416.2 x 67.0 x 20.0 mm
