falkien/Sunlu_S8_Switchwire_Conversion/STL's/X axis/xz_block_left_b_alt.stl

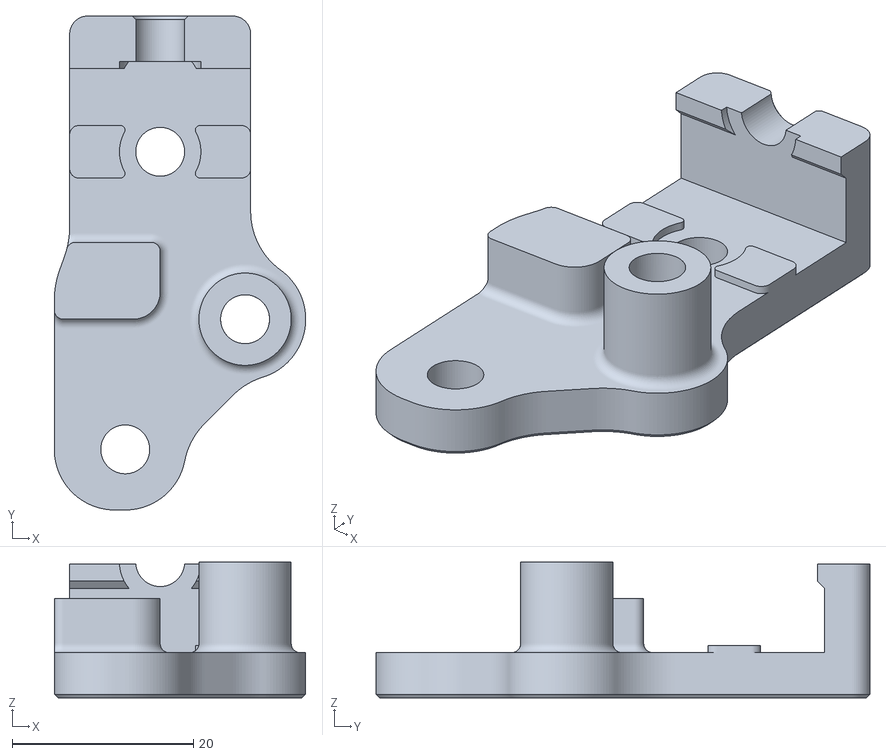
[picture p83: CAD file, 2024-01-11]
STL's/X axis/xz_block_left_b_alt.stl
27.8 x 54.6 x 15.0
