falkien/Sunlu_S8_Switchwire_Conversion/STL's/Z axis/z_bearing_block_right_generic.stl

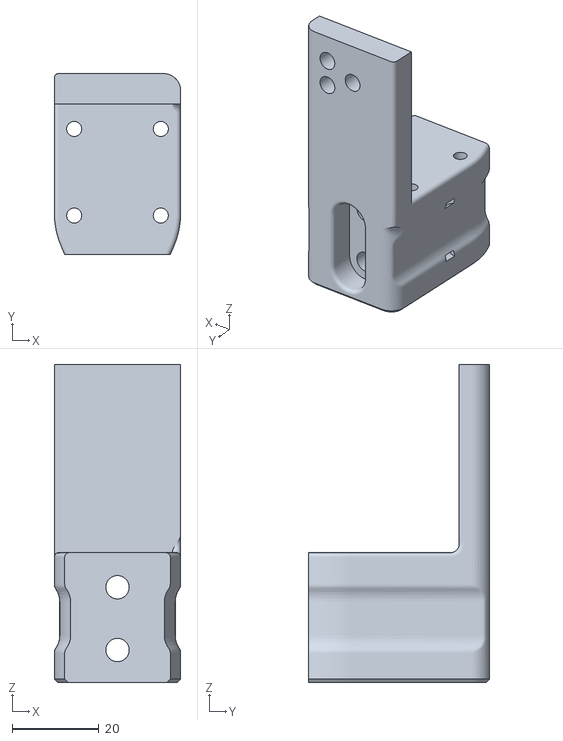
[picture p84: CAD file, 2024-01-11]
STL's/Z axis/z_bearing_block_right_generic.stl
29.2 x 41.8 x 73.4
