falkien/Sunlu_S8_Switchwire_Conversion/STL's/Skirt_New/Sunlu-S8_Switchwire-Feet-V1-A+B_2x.3mf

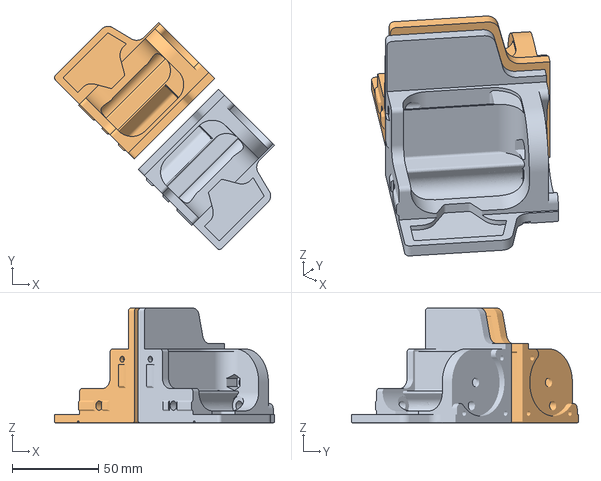
[picture p85: CAD file, 2024-07-27]
STL's/Skirt_New/Sunlu-S8_Switchwire-Feet-V1-A+B_2x.3mf
127.8 x 131.8 x 66.7 mm
CornerA-V1.stl
FootB
