falkien/Sunlu_S8_Switchwire_Conversion/STL's/Z axis/keybak_gantry_anchor.stl

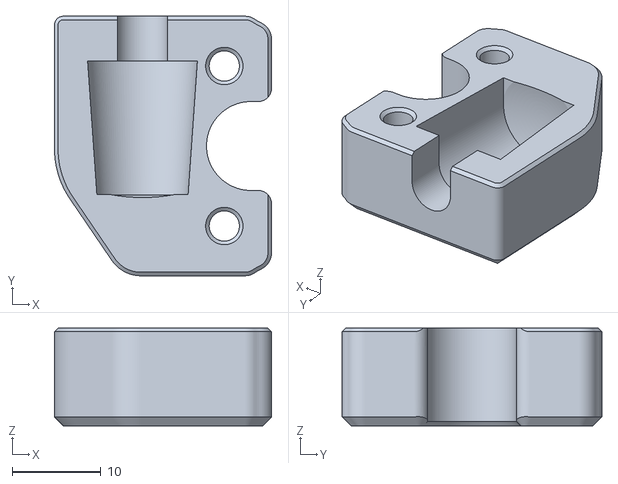
[picture p86: CAD file, 2024-01-11]
STL's/Z axis/keybak_gantry_anchor.stl
24.4 x 29.2 x 11.0
