falkien/Sunlu_S8_Switchwire_Conversion/STL's/Electronics_Bay/Switchwire_Sunlu_S8_RPI4_PSU_Mount.step

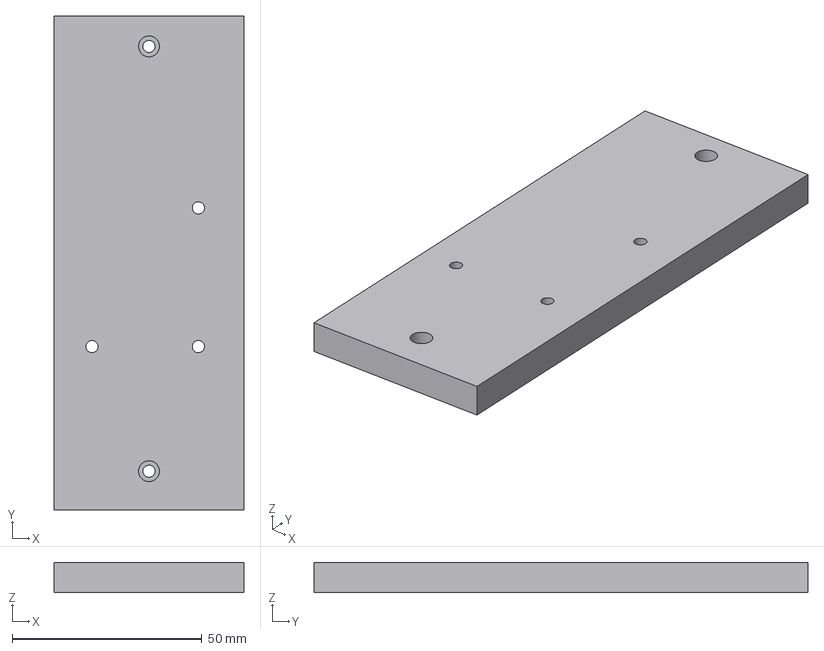
[picture p87: CAD file, 2024-08-11]
STL's/Electronics_Bay/Switchwire_Sunlu_S8_RPI4_PSU_Mount.step
50.0 x 130.0 x 8.00 mm
