falkien/Sunlu_S8_Switchwire_Conversion/STL's/X axis/xz_block_left_a_alt.stl

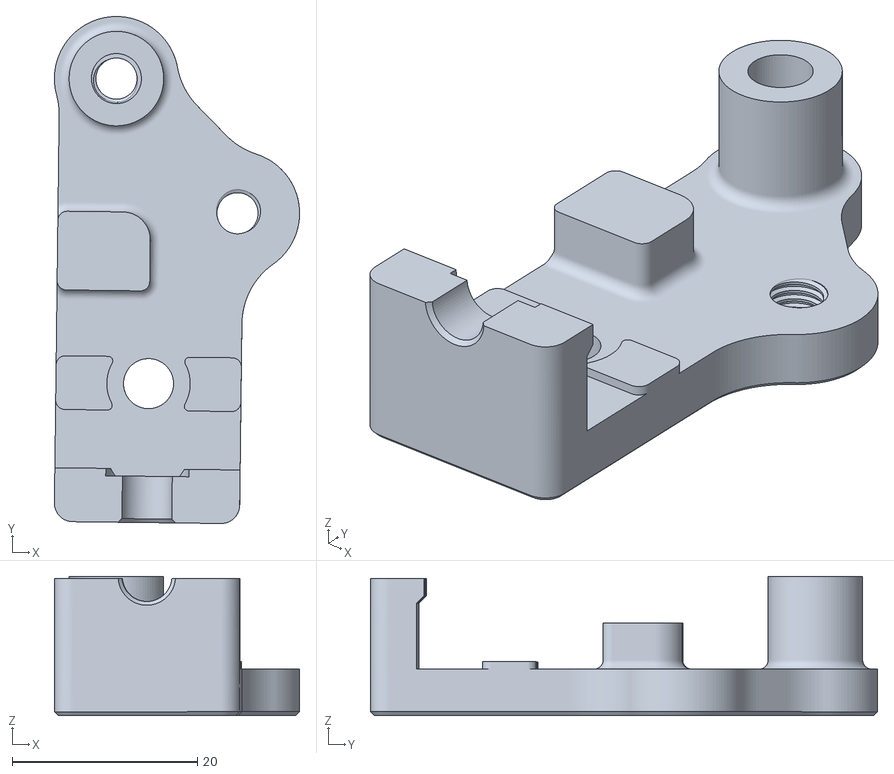
[picture p88: CAD file, 2024-01-11]
STL's/X axis/xz_block_left_a_alt.stl
26.5 x 54.7 x 15.0
