falkien/Sunlu_S8_Switchwire_Conversion/STL's/Z axis/[a]_xz_cable_cover.stl

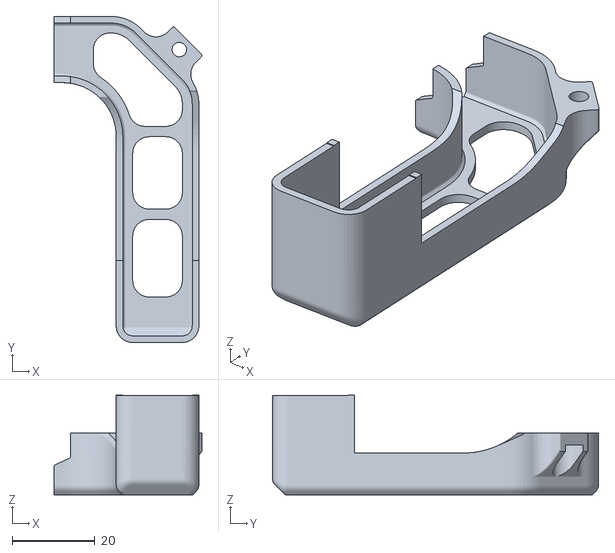
[picture p89: CAD file, 2024-01-11]
STL's/Z axis/[a]_xz_cable_cover.stl
35.7 x 78.8 x 24.1
