falkien/Sunlu_S8_Switchwire_Conversion/STL's/Electronics_Bay/Switchwire_Sunlu_S8_SKR3_Mini_v3_Mount.step

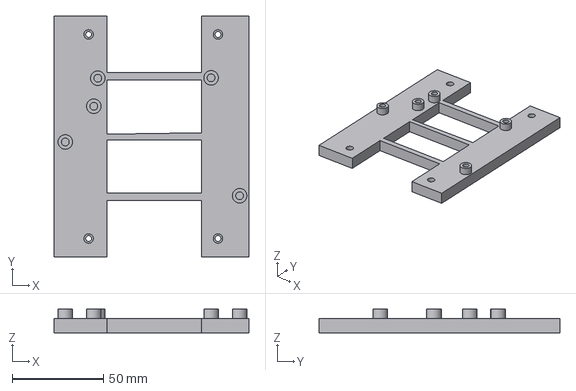
[picture p90: CAD file, 2024-08-11]
STL's/Electronics_Bay/Switchwire_Sunlu_S8_SKR3_Mini_v3_Mount.step
107.0 x 132.0 x 13.0 mm
Sketches
SKR3_Mini3_v3_Mount
