falkien/Sunlu_S8_Switchwire_Conversion/STL's/Electronics_Bay/Switchwire_Sunlu_S8_RPI4_Mount.step

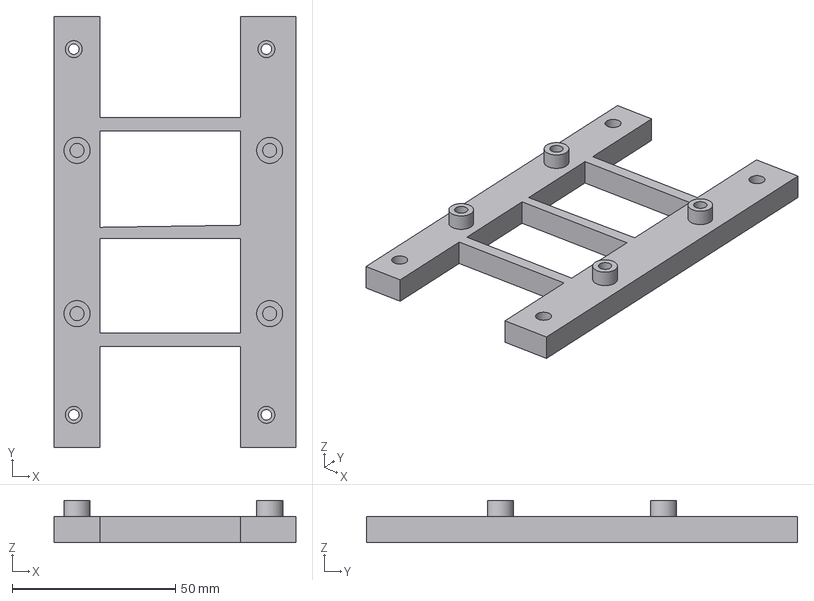
[picture p91: CAD file, 2024-08-11]
STL's/Electronics_Bay/Switchwire_Sunlu_S8_RPI4_Mount.step
74.0 x 132.0 x 13.0 mm
