falkien/Sunlu_S8_Switchwire_Conversion/STL's/X axis/Sunlu_[a]_XZ_belt_clip_x2.stl

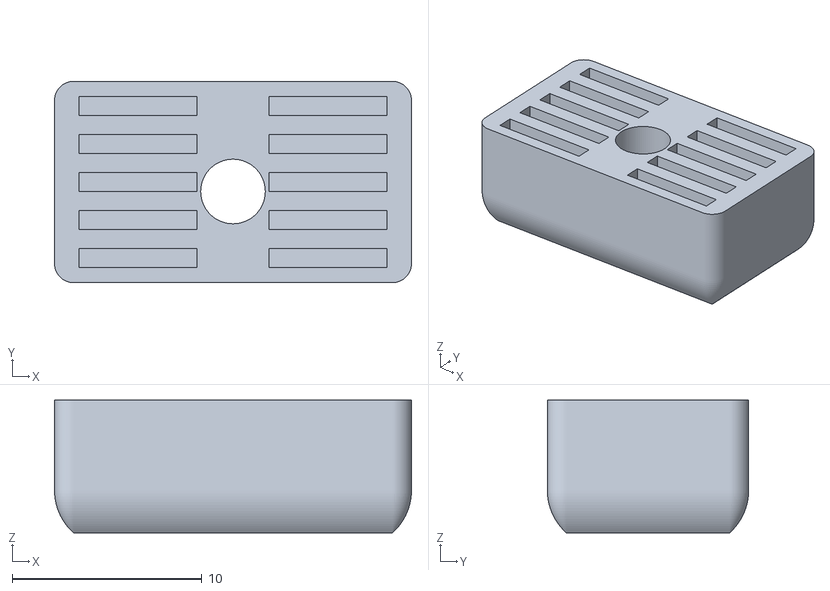
[picture p92: CAD file, 2024-01-11]
STL's/X axis/Sunlu_[a]_XZ_belt_clip_x2.stl
18.8 x 10.6 x 7.00
