falkien/Sunlu_S8_Switchwire_Conversion/STL's/Z axis/z_bearing_block_left.stl

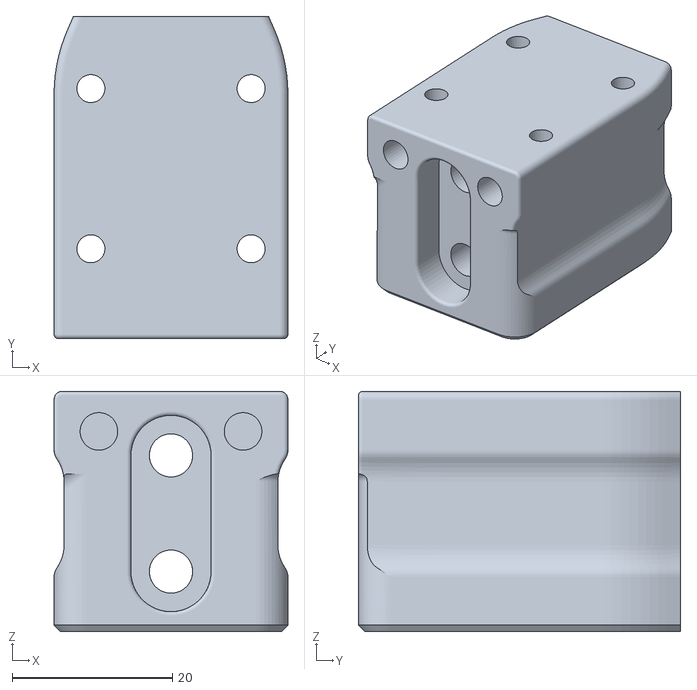
[picture p93: CAD file, 2024-01-11]
STL's/Z axis/z_bearing_block_left.stl
29.2 x 40.2 x 30.0
