falkien/Sunlu_S8_Switchwire_Conversion/STL's/X axis/[a]_upper_idler_support_b_right_original.stl

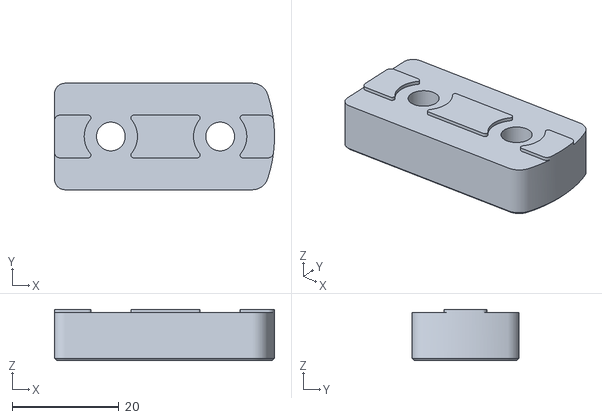
[picture p94: CAD file, 2024-01-11]
STL's/X axis/[a]_upper_idler_support_b_right_original.stl
41.3 x 20.0 x 9.60
