falkien/Sunlu_S8_Switchwire_Conversion/STL's/X axis/upper_idler_support_a_left_new.stl

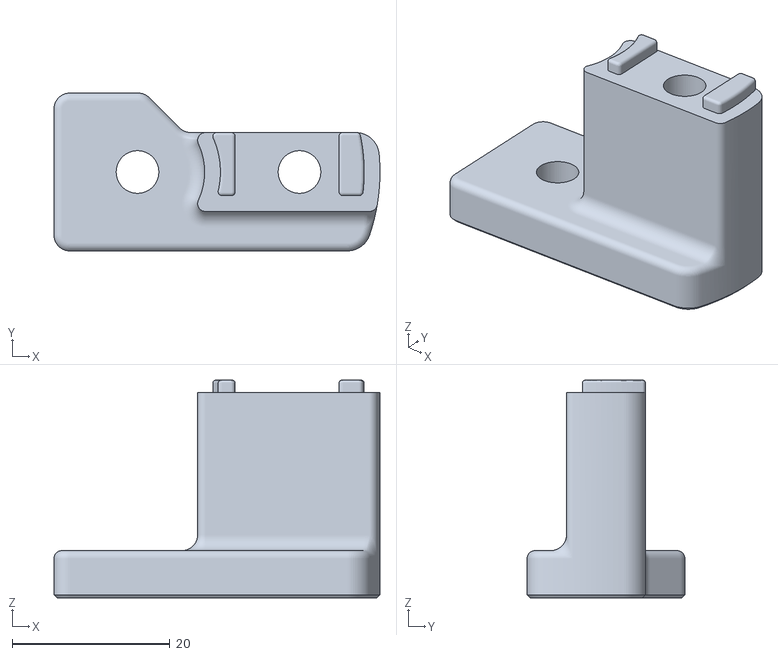
[picture p95: CAD file, 2024-01-11]
STL's/X axis/upper_idler_support_a_left_new.stl
41.3 x 20.0 x 27.6
