falkien/Sunlu_S8_Switchwire_Conversion/STL's/X axis/Sunlu_[a]_X_bearing_block.stl

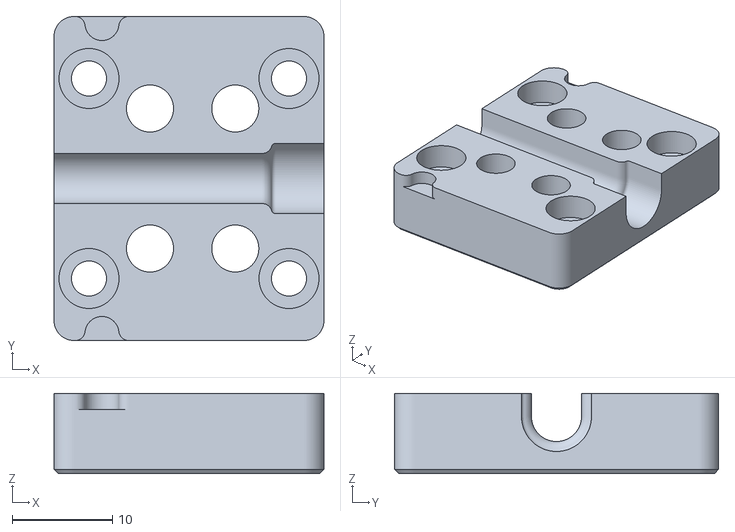
[picture p96: CAD file, 2024-01-11]
STL's/X axis/Sunlu_[a]_X_bearing_block.stl
27.0 x 32.4 x 8.00
