falkien/Sunlu_S8_Switchwire_Conversion/STL's/X axis/Sunlu_probe_retainer_bracket.stl

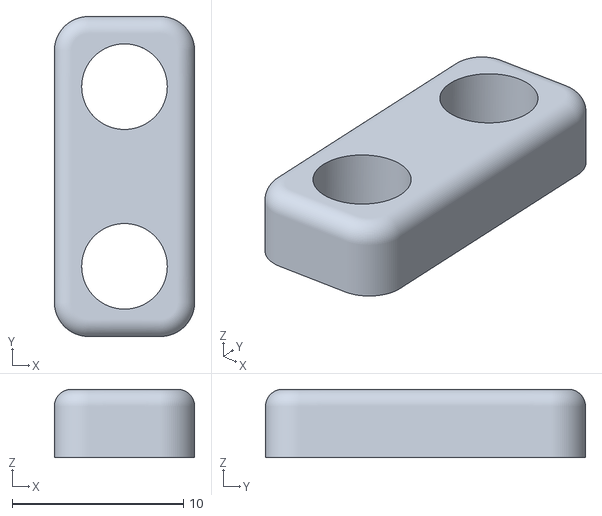
[picture p97: CAD file, 2024-01-11]
STL's/X axis/Sunlu_probe_retainer_bracket.stl
8.20 x 18.7 x 4.00
